ishergin/oxidali/documentation/product-design/bdd/README.md

# BDD

Исполняемые BDD-сценарии — приёмочный канон продукта: поведение собранного
хост-стека, проверенное снаружи.

Границы: в этом каталоге лежит только [реестр ID-префиксов](ids-registry.md). Сами
сценарии — `tests/dali2rust-bdd/features/`; правила слоя (граница чёрного ящика, дерево
фич, теги, трассировка шагов, гейты) — [`05-testing-and-bdd.md`](../../architecture/05-testing-and-bdd.md);
запуск — [`tests/dali2rust-bdd/README.md`](../../../tests/dali2rust-bdd/README.md).
