ishergin/oxidali/documentation/product-design/runtime-modules/mqtt-home-assistant/README.md

# Модуль MQTT Home Assistant

Мост к Home Assistant по MQTT: анонсирует сущности (discovery), публикует их состояние
после коммитов реестра и превращает команды из Home Assistant в семантические команды
шины.

Границы: настройки моста и ручной переанонс — [`../../rest-api/resources/settings-home-assistant.md`](../../rest-api/resources/settings-home-assistant.md);
поведение пары контроллеров — [`../redundancy/README.md`](../redundancy/README.md).
Код — `dali2rust-mqtt-runtime` (воркер, сессия, клиент брокера на ESP-IDF и мок); JSON
Home Assistant строится только в `dali2rust-api/src/ha/`, runtime-крейт несёт готовые
строки.

## Сущности

- Одно устройство Home Assistant на контроллер (`controller_id`). Мост публикует весь
  контроллер: события шины по адаптеру он не фильтрует, адаптер входит в каждый топик.
- **Лампа** — `light` на виртуальную лампу; **группа** — `light` на DALI-группу;
  **выбор сцены** — `select` на адаптер; **устройства ввода** — `event`,
  `binary_sensor` или `sensor` на инстанс, за двумя гейтами: глобальным
  `expose_input_devices` и пер-устройственным `ha_expose`. Физические устройства своих
  сущностей не имеют.
- `unique_id` строится из `controller_id`, адаптера и идентичности ресурса
  (`…_a0_vl_12`, `…_a0_group_7`, `…_a0_scene_select`) и от привязки не зависит:
  перепривязка лампы сущность не меняет.
- Capability группы — объединение по членам; состояние группы сообщает каждый
  цветовой режим, который объявляет её discovery, а у смешанной группы цвет не
  утверждает вовсе.

## Входы и выходы

- **События** (`MQTT_WORKER_HANDLED_EVENTS`):
  `RuntimeStateChangedEvent` — состояние лампы и группы;
  `DaliInputEventObservedEvent` — нажатие или переход датчика;
  `InputDeviceChangedEvent` — переанонс сущностей устройства ввода;
  `PhysicalDeviceChangedEvent`, `VirtualLampChangedEvent` — переанонс ламп (capability
  могли сдвинуться) и пометка групп адаптера;
  `GroupChangedEvent` — переанонс группы; `GroupMatrixChangedEvent` — проход по всем
  группам адаптера (событие не называет, какие сдвинулись);
  `SceneChangedEvent` — переанонс выбора сцены.
- **Команды**: `HomeAssistantDiscoveryPublishCommand` — ручной переанонс (операция
  `ha_discovery_publish`, итог — `HomeAssistantDiscoveryPublishedEvent`);
  `MqttPublishCommand` — публикации правил, за ограничителем (четыре подряд, затем одна
  в секунду; отброшенное считается).
- **Публикует на шину** `DaliSetTargetStateCommand` (лампа, группа) и
  `DaliRecallSceneCommand` (broadcast) с `Origin::Mqtt`: на проводе это `Attended` —
  ползунок web UI обгоняет Home Assistant, а две команды Home Assistant друг друга не
  вытесняют.
- **Триггеры правил** (`when mqtt`): топики мост читает из read-порта стора правил,
  когда сдвигается поколение документа. Сообщение на таком топике — `MqttRuleMessageEvent`
  через `publish_required`, а не команда Home Assistant; топик, который заодно командный,
  — и то и другое ([`ADR-033`](../../../architecture/decisions/ADR-033-mqtt-rule-trigger.md)).
  Темп задаёт мост: не больше одного события на топик за `RULE_MESSAGE_INTERVAL_MS`
  (100 мс) — первое сообщение уходит сразу, следующее ждёт конца интервала, а более новое
  заменяет ждущее. Сообщение не переживает свою сессию: конец сессии выбрасывает и
  ждущее темпа, и то, что ещё стоит в очереди клиента; ждущее выбрасывает и снятие его
  топика из документа. Счётчики блока `mqtt` в `/api/v1/stats`: `rule_messages_total`,
  замещённые `rule_messages_coalesced_total` и потерянные `rule_messages_lost_total` —
  отказ шины после отката или выброшенное сообщение; всё, что не дошло до правил, кроме
  retained-ответа на подписку и потерянного очередью клиента (`commands_dropped_total`,
  §Надёжность), попадает в один из двух последних.
- **Настройки** перечитываются из read-порта, когда сдвигается счётчик применения
  настроек Home Assistant: его двигают запись настроек и перезагрузка слайсов (импорт,
  репликация). На событие настроек мост сознательно не подписан. Пароль брокера —
  отдельный порт.

## Сессия

- **Сессия есть**, только если мост включён, брокер задан и контроллер активен:
  стэндбай и выключенный мост ведут себя одинаково — отключиться, выбросить шину,
  ничего не публиковать. Возврат идёт тем же дозвоном.
- **Переподключает только мост.** Клиент на устройстве — esp-mqtt без обёртки esp-idf-svc
  ([известные дефекты](../../known-issues.md) ISSUE-138), и его собственное
  переподключение выключено: обрыв и неудачный дозвон дают событие отключения, и мост
  звонит заново новым клиентом.
- **Свежая сессия переанонсирует всё**, включая уборку снятых сущностей: retained-
  сообщения — память брокера, а не наша, и брокер без персистентности теряет их при
  рестарте. План тот же, что у ручного переанонса; прерванный обрывом план переносит
  свою операцию в новый прогон. Прогон, который запланировала сама сессия, ни в какую
  операцию не отчитывается и пропускает сущности, уже опубликованные в этой сессии байт
  в байт; ручной переанонс публикует всё заново, не сверяясь с кешем сессии.
- **Смена `controller_id` или префиксов** закрывает сессию: мост публикует `offline` на
  прежнем топике доступности и переанонсирует всё под новыми топиками. Уборка идёт
  только под текущими топиками, поэтому retained-конфиги прежнего `controller_id`
  остаются на брокере осиротевшими: Home Assistant показывает их недоступными, пока их
  не удалят вручную.
- **Топики правил**: свежая сессия подписывает их (QoS 0) следом за командными
  топиками Home Assistant, а смену документа мост досинхронизирует в живой сессии —
  новые подписывает, снятые отписывает. Топик правила, который уже покрывает командный
  фильтр, своей подписки не получает: брокер вправе прислать копию на каждую подходящую
  подписку, и Mosquitto так и делает. Топик, который мост публикует сам (состояние,
  доступность, discovery), он не подписывает вовсе: отказ пишется в лог с топиком,
  считается в `own_topics_refused_total` раз за сессию, сами топики сессии видны в
  `/api/v1/controller`, и флаг `connected` отказ не держит.
  Сообщение, которое брокер доставил с флагом retain, то есть в ответ на саму подписку,
  мост правилам не передаёт (правила —
  [`../rules-engine/mqtt-trigger.md`](../rules-engine/mqtt-trigger.md)).
- **`connected` означает, что брокер может доставить нам всё, на что сессия
  подписывается**: флаг поднимается, когда подписки сессии, топики правил включительно,
  отправлены и подтверждены (SUBACK), а не на CONNACK, и опускается, пока новый топик
  правила ждёт своего SUBACK; SUBACK находит свою подписку по message id. Сверка держится
  на том, что клиент на устройстве выдаёт id по порядку (`CONFIG_MQTT_MSG_ID_INCREMENTAL`
  в `sdkconfig.p4.defaults`): со случайными id две подписки одной сессии, ждущие SUBACK,
  могли бы получить один id, и SUBACK одной закрыл бы другую. Отказ брокера
  в подписке (SUBACK 0x80) держит флаг опущенным, пока отказанный топик остаётся в
  документе правил, а отказ командному фильтру — до конца сессии; каждый отказ
  считается в `subscriptions_refused_total` и пишется в лог с топиком.
- **Доступность**: last will регистрируется в сессии, retained `online` публикуется до
  любого discovery; сознательное отключение сначала публикует `offline`. Лампа объявляет
  два источника доступности — контроллер и себя (`availability_mode: all`), поэтому её
  топик доступности публикуется вместе с конфигом discovery: пока он молчит, Home
  Assistant держит сущность недоступной.
- **Уборка всегда retained**: пустой payload снимает retained-конфиг, только если сам
  несёт флаг retain. Снятие лампы стирает не только её конфиг, но и retained-доступность
  и состояние: лампа, заново созданная под тем же id, иначе унаследовала бы чужие
  `online` и уровень.
- Discovery публикуется размеренно, а не пачкой; переанонс проверяется по хешу, так
  что неизменившиеся конфиги брокер не видит. Глубокий инбокс коалесцирует события по
  сущности.
- Транспорт — `mqtt://` без TLS.

## Граница формата

- **Уровень**: в реестре и на шине — сырой arc power `0..254`; шкала `brightness`
  Home Assistant существует только в MQTT-payload'е, перевод — на границе. Включённая
  лампа с неизвестным уровнем публикуется без `brightness`, а не с нулём; включение
  без яркости — `GO TO LAST ACTIVE LEVEL` в гире.
- **Цветовая температура**: JSON-схема Home Assistant несёт её ключом `color_temp`;
  discovery объявляет `color_temp_kelvin: true`, поэтому значение — в кельвинах. Ключ
  `color_temp_kelvin` в payload'е не читается и не пишется: это имя флага discovery.
  Диапазон `min_kelvin` / `max_kelvin` объявляет только лампа — у группы честного
  диапазона нет.
- Проверки значений — общий разбор уставки, тот же, что у REST.

## Плитка группы

Групповая сущность показывает ON, только если группе **командовали** включение и хотя
бы один её applied-член горит. «Командовали» — групповой или широковещательный факт
питания от нас (Home Assistant, web UI, REST, HCL, правила) или групповой кадр чужого
мастера; broadcast взводит и снимает флаг всем группам; recall сцены и команда только
цвета флаг не трогают. Флаг волатилен: после перезагрузки плитки говорят OFF до первой
групповой команды.

## Надёжность

Доставки at-least-once для discovery и состояния нет: состояние догоняет следующий
коммит, конфиги — хеш-гейт и переанонс свежей сессии. Счётчики — блок `mqtt` в
`/api/v1/stats` и `/api/v1/diagnostics`. `commands_dropped_total` считает всё входящее,
что потеряла очередь клиента (16 сообщений), сообщения на топиках правил тоже: очередь
стоит до разбора топика. Туда же идёт команда Home Assistant, пришедшая в сессии, которая
кончилась до её разбора: после переподключения она не исполняется, как и сообщение для
правил. Сообщение, которое брокер ещё нёс по топику, только что
снятому с подписки, приходит, когда топика уже нет среди правил, и считается принятой
неразмаршрутизируемой командой.

## Тесты

Чёрный ящик через мок брокера (`tests/dali2rust-bdd/features/mqtt_home_assistant/`):
discovery, состояние, команды, цвет, группы, триггеры переанонса; триггер правил
`when mqtt` — в `tests/dali2rust-bdd/features/rules/`. Формат payload'ов —
unit-тесты `dali2rust-api/src/ha/`; сессия и планы — крейт-тесты моста.
