ishergin/oxidali/documentation/product-design/runtime-modules/redundancy/README.md

# Модуль redundancy

Два контроллера на одном сегменте DALI: второй молчит, пока первый жив, и берёт шину,
когда тот перестаёт отвечать. Обнаружение — не наше изобретение: DiiA 351 §7 описывает
единственный арбитраж двух application controller'ов на одном сегменте, который в
экосистеме DALI есть.

Границы: решение и его поправки — [`ADR-018`](../../../architecture/decisions/ADR-018-controller-redundancy.md);
ответ в окне backward-кадра на уровне PHY — [`../../../architecture/08-dali-phy-and-transport.md`](../../../architecture/08-dali-phy-and-transport.md);
REST — [`settings-redundancy`](../../rest-api/resources/settings-redundancy.md),
[`redundancy`](../../rest-api/resources/redundancy.md),
[`policies`](../../rest-api/resources/policies.md),
[`config-transfer`](../../rest-api/resources/config-transfer.md); UI —
[`../../web-ui/redundancy.md`](../../web-ui/redundancy.md). Код —
`dali2rust-redundancy-runtime` (воркер арбитража, супервизор лизы, воркер репликации).

## Роли

351 §5 знает четыре типа устройства, и арбитраж исполняет только type B; types A и C
никогда не спрашивают и не уступают, а лишь отвечают.

| Роль | 351 | Поведение |
|---|---|---|
| `primary` | A / C | не зондирует, активен, пока жив |
| `standby` | B | зондирует, уступает на любой ответ, берёт шину на молчание |

Выборов между равными нет — в спецификации их нет. Пара из двух `standby` допустима и
разводится разницей во времени старта узлов; случайного сдвига нет. Стэндбай, взявший
шину, продолжает зондировать и уступает, как только первичный снова отвечает.
`applicationActive` хранится в NVM, поэтому перезагрузка переключения не отменяет:
погашенный первичный остаётся погашенным, пока его не включат, и обратно не зондирует.

**Сеть роль не двигает.** Воркер арбитража не читает сетевого состояния вовсе:
потеря Ethernet, брокера или HTTP пира роль не двигает ни в какую сторону. Обратное
тоже верно: арбитраж не спасает от отказа блока питания шины, обрыва или замыкания.

## Обнаружение

Стэндбай широковещательно шлёт 24-битный `QUERY APPLICATION CONTROLLER ENABLED` на
приоритете 5 и читает ответ как type B: **любой ответ, включая испорченный**, — у шины
есть хозяин; молчание — нет. Зонд, который не удалось передать (коллизия, занятая
шина), — не молчание и не вердикт. На выключенном адаптере зонд не отправляется вовсе, а
неотправленный зонд — не промах: стэндбай с выключенным адаптером шину не берёт. Почему
не взятие шины по тишине —
[`ADR-018`](../../../architecture/decisions/ADR-018-controller-redundancy.md).

## Ответ

Первичный обязан ответить в окне Table 20. Супервизор заранее кладёт пары «образ кадра →
байт ответа» в таблицу (`dali2rust-platform::arbitration`): это
`QUERY APPLICATION CONTROLLER ENABLED` в широковещательной форме и по собственному
адресу, а без короткого адреса — в форме broadcast unaddressed. Решает задача сниффера,
передаёт прерывание PHY —
[`../../../architecture/08-dali-phy-and-transport.md`](../../../architecture/08-dali-phy-and-transport.md)
§Answering inside Table 20.

Новый запрос — это слот, а не ветвление. Последовательность, чей ответ зависит не от
одного кадра (`READ MEMORY LOCATION` с DTR, `COMPARE` в поиске), таблицей выразить
намеренно нельзя. `applicationActive = false` даёт **пустую** таблицу, а не ответ NO:
NO в DALI — это отсутствие кадра, и потому два стэндбая не могут ответить друг другу и
застыть оба пассивными.

## Лиза живости

Арбитраж доказывает, что жив отвечающий блок, а не что контроллер работает. Поэтому
супервизор раз в секунду продлевает таблицу на 3 с, пока **реестр**, **планировщик HCL**
и **движок правил** провернулись за последние 3 с. Застрявший воркер перестаёт быть
представленным, лиза истекает, ответы прекращаются, и следующий зонд стэндбая находит
шину бесхозной. Механизм отказа — вызов, которого не происходит: ничто ничего не
отзывает, и застрявший супервизор даёт тот же исход. Воркер, который ещё ни разу не
провернулся, живым не считается; воркер в ограниченном ожидании — провернулся: «занят»
не значит «завис». Все читатели лизы берут время у часов супервизора.

`DaliWorker` не наблюдается: на тихой шине он законно спит на инбоксе, а один скан
законно держит его десятки секунд — окно по оборотам либо срабатывало бы на здоровом
скане, либо не значило бы ничего.

Супервизор читает `applicationActive` прямо из хранилища реестра, а не из подписки на
шину: решение раз в секунду обязано приниматься и на насыщенной шине, когда подписка
отстаёт. Событие настроек DALI лишь будит его раньше срока.

## Бюджет времени

| Величина | Формула | По умолчанию |
|---|---|---|
| Обнаружение отказа | порог промахов × период зонда + один зонд | порог 2, период 400 мс: ≤ 0,86 с |
| Переключение роли | флип `applicationActive`, старт HCL и поллера | < 100 мс |
| Плановое переключение | пара `ENABLE`, опрос транслятора, реестр | < 100 мс, свет не меняется |
| Цена провода | ≈ 38 мс активного провода на зонд | ≈ 9,5 % на приоритете 5 |
| Застрявший воркер → молчание | порог застоя + TTL лизы | ≤ 6 с |

Приоритет 5 — самое низкое окно Table 22: зонд уступает всему, что делает оператор.
Порог по умолчанию не выбран — открытый ISSUE-86 в
[`../../known-issues.md`](../../known-issues.md).

## Пассивный контроллер

| Подсистема | На пассивном |
|---|---|
| Провод | любой forward-кадр отказывает `controller_passive` у единственного владельца провода; HTTP отвечает `409 controller_standby` с `Retry-After: 1` |
| Зонд арбитража | идёт — единственное исключение |
| HCL | тик считается, ничего не публикуется |
| Поллер | цикл считается, список целей пуст |
| Мост MQTT | сессии с брокером нет: пара делит `controller_id`, и подключённый стэндбай дрался бы с активным за сущности |
| REST-чтения, WebSocket | работают |

HCL и поллер гасятся ради счётчиков, а не ради провода: провод и так защищён гейтом, а
растущие `command_failures` на правильно себя ведущем контроллере читать невозможно.

**Роль видна** — заголовок и `role` в `/api/v1/health`
([`redundancy`](../../rest-api/resources/redundancy.md)), значок в web UI, буква на OLED
([`display`](../display/README.md)): для звонящего ответы стэндбая истинны и бесполезны,
и без роли «лампа не изменилась» неотличимо от «я говорю не с тем узлом».

## Плановое переключение

Шаги, их порядок и ответы — контракт
[`redundancy`](../../rest-api/resources/redundancy.md) §`POST /redundancy/switchover`.

`Dali103HandoverSentEvent` публикуется до команды ухода в пассив: отдающий узел
записывает переход как `handover`, только если это событие пришло к воркеру арбитража
раньше смены `applicationActive`; принимающий — потому что флаг сдвинул провод. Флаг и
причину его последней смены воркер читает одним вызовом под одной блокировкой
(`application_active_moved_by`): причина, пришедшая событием, отстаёт от флага, и
плановая передача записалась бы как `manual`.

## Перенос конфигурации

Runtime стэндбай получает со сниффера, конфигурацию — с пира (почему так и почему не
MQTT — [`ADR-018`](../../../architecture/decisions/ADR-018-controller-redundancy.md);
что переносится — [`config-transfer`](../../rest-api/resources/config-transfer.md)).
Пассивный контроллер с заданным `peer_url` раз в 30 с тянет у пира манифест слайсов
(`GET /api/v1/config/slices`: имя, размер, CRC), забирает слайсы, чьи размер или CRC
отличаются, кладёт их одной партией в стейдж импорта реестра и публикует **один**
`RegistrySliceReloadCommand` на проход; воркер реестра пишет слайсы, которые
декодируются, и перечитывает реестр, а отвергнутые считает в
`persistence.hydrate_error_total` `/api/v1/diagnostics`
([config-transfer](../../rest-api/resources/config-transfer.md) §Импорт).

- Тянет только пассивный: активный — источник истины пары.
- Порядок пира — порядок гидрации: физические устройства раньше ламп.
- Слайс, которого у пира нет, пропускается, а не удаляется.
- Один reload на проход: reload между двумя слайсами гидрировал бы наполовину
  импортированный набор.
- Недостижимый пир считается и остаётся пиром; роль от этого не меняется.

## Счётчики

Блок `arbitration` в `GET /api/v1/redundancy`:

- `defended` — тики супервизора (раз в секунду), на которых лиза продлена: узел активен
  и все наблюдаемые воркеры крутятся. На пассивном узле не растёт.
- `worker_stale` — тики, на которых лиза не продлена из-за воркера, который встал или
  ещё ни разу не провернулся. Сразу после загрузки счётчик может быть ненулевым: тик
  супервизора успевает раньше первого оборота воркера, и это не отказ.
- `answered` — ответ на чужой зонд дошёл до провода; `suppressed` — зонд узнан и не
  отвечен.
- `cell_busy`, `aborted`, `window_closed` — ответ не ушёл: ячейка PHY занята, передачу
  прервали, окно закрылось; `late` — ответ опоздал.
- `probe_failed` — наш зонд не дошёл до провода; `handover_incomplete` — плановое
  переключение не завершилось.

Журнал переходов (последние восемь, с причинами и метками) — там же, `transitions`.
