ishergin/oxidali/documentation/product-design/runtime-modules/state-fanout/README.md

# Модуль state-fanout

Проектор runtime-фактов: единственный продовый издатель `RegistryRuntimeUpdateCommand`.
Превращает типизированные факты о шине — наша команда исполнена, сцена вызвана, чужой
кадр увиден, устройство прочитано — в коммиты runtime-состояния, раскрывая группы,
broadcast и сцены по участникам.

Границы: как реестр сливает коммит — [`../../../architecture/06-registry-and-persistence.md`](../../../architecture/06-registry-and-persistence.md);
контракт RRUC — [`../../bus-contracts/commands.md`](../../bus-contracts/commands.md)
§Runtime-команды реестра; откуда берутся наблюдения —
[`../sniffer-translator/README.md`](../sniffer-translator/README.md). Код —
`projector_worker` в `dali2rust-fanout-runtime`.

## Входы и выходы

- **Потребляет**: `DaliTargetStateAppliedEvent`, `DaliSceneRecalledEvent`,
  `DaliObservedFrameEvent`, секцию `RuntimeStatus` из `DaliAttributesReadEvent` и
  `DaliAttributeReadOutcomesEvent` (устройство не ответило).
- **Публикует** только `RegistryRuntimeUpdateCommand` и
  `RegistryLevelTransitionCommand`, через `publish_required`. DALI-команд не
  публикует, в реестр напрямую не пишет, активацию сцены не синтезирует.
- **Читает** `ProjectorReadPort`: привязки, applied-членство групп, applied-строки
  сцен, capability ламп.

## Правила раскрытия

| Факт | Раскрытие |
|---|---|
| Наша команда по лампе или короткому адресу | одна запись с обеими идентичностями — один физический коммит |
| Наша команда или чужой кадр на группу | привязанные лампы — **applied**-члены группы |
| Broadcast | все привязанные лампы адаптера |
| Recall сцены (наш или чужой), broadcast | только **applied**-строки сцены; desired-only строки не проецируются |
| Recall сцены на группу | applied-строки сцены, чьи лампы — applied-члены группы |
| Recall сцены на короткий адрес (наш — на лампу — или чужой) | applied-строка лампы, привязанной к адресу |
| Чужой кадр по короткому адресу | лампа, привязанная к адресу, и само устройство |
| Арк-команда без уровня (`LevelTransitionObserved`) | `RegistryLevelTransitionCommand` на каждого участника; уровень считает реестр |
| Секция `RuntimeStatus` чтения | один коммит устройства |
| Исход чтения «устройство не ответило» | наблюдение отсутствия (`device_absent`) без уровня и без `last_seen_ms` |

- **Recall** — наш и чужой — раскрывается из одного `DaliSceneRecalledEvent`: чужой
  `GO TO SCENE` транслятор публикует только этим фактом
  ([`../sniffer-translator/README.md`](../sniffer-translator/README.md)).
- **Цветовой гейт** при раскрытии на разнородных участников —
  [`../../../architecture/06-registry-and-persistence.md`](../../../architecture/06-registry-and-persistence.md)
  §Colour capability gate; capability участника берётся из вида лампы, то есть с учётом
  override устройства.
- **Коалесинг**: подряд идущие наблюдения сниффера с целевым состоянием
  (`TargetStateObserved`) на одну цель `(адаптер, scope, идентичность)` копятся в
  буфере — чужой фейд не заливает инбокс реестра. Новое наблюдение выбрасывает из
  буфера те, что повторяет целиком: уровень, цвет того же режима, факт DAPC и ненулевой
  уровень, от которого реестр ведёт `lastActiveLevel` (102 §9.4). Остальные уходят по
  порядку, каждое своим коммитом со своей меткой, и реестр упорядочивает их против
  собственных коммитов: фейд уровня и цветовой температуры вперемежку сворачивается до
  последнего факта каждого измерения, уровень DAPC и цвет следующего за ним `ACTIVATE`
  приходят оба, затухание до нуля оставляет последний горевший уровень, а цвет группы в
  другом режиме не стирает прежний у участника, который этот режим не принимает. Буфер
  ограничен: переполнение отправляет самое раннее наблюдение. Арк-команды без уровня
  (`LevelTransitionObserved`) не сворачиваются: каждая — отдельный переход. Любой
  другой факт или другая цель сначала сбрасывают буфер, поэтому порядок относительно
  наших фактов сохраняется.
- **Пейсинг**: раскрытие публикуется пачками по восемь с короткой паузой и делит один
  бюджет ретраев на всё раскрытие (`ADR-007`, `ADR-021`).

## Корреляция и источник

- Какие факты несут корреляцию запроса, а какие `CORRELATION_NONE`, и как проброшенная
  монотонная метка упорядочивает наблюдения —
  [`../../../architecture/06-registry-and-persistence.md`](../../../architecture/06-registry-and-persistence.md)
  §Update path и §Merge rules. Метка applied-факта — момент применения на проводе;
  отсутствие не штампуется.
- Источник коммита команды — из её `Origin` (`Api`, `Mqtt`, `Hcl`, `Rules`): `DaliWorker`
  кладёт его в `source` applied-факта и recall-факта рядом с `hold_hcl` команды, и оба
  проектор переносит в каждую запись раскрытия. Наблюдения сниффера — `Sniffer`;
  секция `RuntimeStatus` — `Readback`: чтение ничего не командует, и HCL не должен
  принимать его за ручное вмешательство; отсутствие устройства — `Poller`. Записи без
  команды за спиной `hold_hcl` не снимают.

## `last_dapc_source`

Проектор — единственный, кто его выставляет:

| Факт с DAPC | Значение |
|---|---|
| Наша команда по лампе или короткому адресу | `unknown` (`null` в JSON) |
| Наша или чужая команда на группу или broadcast | `group` |
| Чужой кадр по короткому адресу | `sniffer` |
| Recall сцены | `scene` |

Факт без DAPC (только цвет, только статус) передаёт `None`, и реестр сохраняет
прежнее значение. HCL различает источники по источнику коммита, а не по этому полю.

## Состояние и тесты

Прочного состояния нет, только буфер коалесинга. Чёрный ящик — `SYS-210..215` и
групповой recall (`tests/dali2rust-bdd/features/system/integration-fanout.feature`):
источники API и сниффер. Раскрытие, гейт цвета, `last_dapc_source`, коалесинг —
крейт-тесты `projector_flow.rs` и `sniffer_translator_flow.rs`: канальный уровень
шины чёрному ящику недоступен.
