ishergin/oxidali/documentation/product-design/runtime-modules/apply-orchestrator/README.md

# Модуль apply orchestrator

Исполняет массовое применение: разворачивает его в ячейки по снапшоту реестра и
публикует их по одной, так что размер применения не связан с глубиной очередей шины.
Решение — [`ADR-007`](../../../architecture/decisions/ADR-007-apply-orchestrator.md).

Границы: HTTP-вход применения (`409`, быстрый путь пустого diff, одна execute-команда)
— [`../api-gateway/README.md`](../api-gateway/README.md); жизненный цикл операции —
[`../operation-tracker/README.md`](../operation-tracker/README.md); исполнение ячеек —
[`../dali-worker/README.md`](../dali-worker/README.md). Код —
`dali2rust-operations-runtime` (воркер и ядро пейсинга `apply_pacing`).

## Семейства

| Execute-команда | Снапшот | Ячейка | Исход ячейки |
|---|---|---|---|
| `GroupApplyExecuteCommand` | desired против applied матрицы групп | `DaliProgramGroupMembershipCommand` на одну пару «лампа × группа» | `DaliGroupMembershipProgrammedEvent` |
| `SceneApplyExecuteCommand` | строки одной сцены | `DaliProgramSceneCommand` на одну строку | `DaliSceneProgrammedEvent` |
| `PolicyApplyExecuteCommand` | политика и список известных устройств | `DaliWriteAttributesCommand` с `signals_operation = false` на одно устройство | `DaliAttributesWrittenEvent` |

Ядро пейсинга общее и о семействе не знает; семейство — это тип ячейки и событие её
исхода. Новое семейство обязано объявить событие исхода в подписке оркестратора, иначе
прогон не получит собственных исходов. Событие исхода приходит на каждую исполненную
ячейку, даже когда ничего не подтвердилось, и его ошибка — исход ячейки; у ячейки
политики недостающее значение без ошибки — `verify_failed` (`policy_not_confirmed`).

## Входы и выходы

- **Читает** `ApplyReadPort` — снапшот **в момент дескью** execute-команды, а не в
  момент HTTP-запроса. Правка desired во время долгого прогона оставляет ресурс dirty
  и требует повторного применения.
- **Потребляет** события исходов своих ячеек; статус своей операции не слушает, а
  опрашивает у трекера (ниже, «Отмена»).
- **Публикует** ячейки, синтетические исходы пропуска и провала и терминальный
  `OperationWorkerSignalEvent` — он один заканчивает операцию, исходы только наполняют
  результат. Исходы и сигнал — через `publish_required`: это единственные носители
  итога. Операцию открывает тот, кто просит применение (HTTP, правило, `DaliWorker`
  после discovery), до execute-команды; оркестратор её не открывает.
- **Не делает**: не мутирует реестр (applied выводит реестр из событий исходов), не
  трогает провод (ячейки исполняет `DaliWorker`, поэтому они видны на шине, в
  сниффере и в счётчиках), не считает статус операции (это трекер).

## Пейсинг

- **Привязанная ячейка — окно в одну**: опубликовать ячейку, дождаться её исхода,
  опубликовать следующую. Такт задаёт сам провод DALI; в полёте не больше одной
  ячейки.
- **Непривязанная лампа провода не занимает**: её исход «пропущено» публикуется
  пачками по восемь — меньше любого инбокса событий — и тактируется собственной
  петлёй.
- **Полная ingress-очередь** — ограниченный backoff (десяток попыток до 250 мс).
  Исчерпание проваливает ячейку синтетическим исходом (`cell_ingress_overload`) или
  обрывает пачку пропусков (`skip_ingress_overload`); прогон идёт дальше и
  заканчивается отказом. Это единственная точка backpressure на пути применения.
- **Ячейка без исхода** за 5 с публикуется повторно один раз (запись и readback
  идемпотентны); второй таймаут публикует синтетический провал, чтобы у ячейки был
  исход в результате, и прогон продолжается — одна упавшая ячейка не останавливает
  применение.
- **Отмена**: прогон раз в 250 мс опрашивает статус своей операции у трекера и
  останавливается, как только она терминальна (TTL, отказ доставки, сброс таблицы); есть и
  собственный дедлайн. Почему опрос, а не событие, — `ADR-007`.

## Корреляция

Ячейки несут корреляцию прогона. Поэтому ячейка политики публикуется с
`signals_operation = false`: её сигнал закрыл бы всю операцию после первого
устройства. Операцию закрывает терминальный сигнал оркестратора после последней
ячейки; программирование групп и сцен сигналов не публикует вовсе.

## Состояние

Прочного состояния нет. Прогоны идут строго последовательно в одном потоке, инбокс
исходов перед стартом дренируется, чтобы поздний исход прошлого прогона не засчитался
текущему. Инбокс команд — четыре кадра: переполнение означает затор execute-запросов и
сразу отвечает отказом доставки.

## Тесты

Чёрный ящик: применение, чей diff больше глубины очередей, проходит через пейсинг и
заканчивается `succeeded` с точными итогами (`GRP-066`). Инварианты очереди — одна
ячейка в полёте, петля пропусков, таймаут → повтор → синтетический исход, backoff,
отмена — крейт-тестом `apply_orchestrator_flow.rs`.
