ishergin/oxidali/documentation/product-design/runtime-modules/dali-worker/README.md

# Модуль dali-worker

Единственный владелец провода: исполняет семантические DALI-команды одного адаптера,
решает, кто кому уступает провод, и публикует типизированные факты о том, что
произошло на шине DALI.

Границы: смысл команд — [`../../bus-contracts/semantic-dali-commands.md`](../../bus-contracts/semantic-dali-commands.md);
протокольные правила (приоритет и прерывание, транзакции, чтение ответов, доказательство
DTR, активация цвета) — [`../../../architecture/09-dali-protocol-rules.md`](../../../architecture/09-dali-protocol-rules.md);
доставка отказов, гарантированная публикация и коалесинг —
[`../../../architecture/03-bus-and-backpressure.md`](../../../architecture/03-bus-and-backpressure.md);
PHY и транспорт — [`../../../architecture/08-dali-phy-and-transport.md`](../../../architecture/08-dali-phy-and-transport.md).

## Входы и выходы

- **Команды**: все виды из `DALI_WORKER_HANDLED_COMMANDS` — управление светом,
  программирование, чтение и обнаружение, коммиссионинг gear, Part 103, арбитраж,
  диагностический сырой кадр. Инбокс — 128 кадров.
- **Читает** `RegistryReadPort`: состояние адаптера для гейта, роль контроллера,
  привязку лампы к короткому адресу (в момент исполнения), известные и свободные
  адреса, политику DT8 для конкретного устройства.
- **Публикует** подтверждения запросам, сигналы операций, результаты DALI и
  applied-факты. `RegistryRuntimeUpdateCommand` не публикует никогда: runtime
  доходит до реестра через проектор state-fanout.
- Crate: `dali2rust-dali-runtime` (воркер, семантический исполнитель, `DaliController`).
  Один воркер на транспорт; в прошивке он один.

## Гейты перед проводом

Проверяются в одной точке диспетча, до любого кадра; как отказ доходит до вызывающего и
почему причина названа — 03 §A refusal needs a listener.

- **Адаптер выключен** (`enabled = false`) — отказ `adapter_disabled` любому виду
  команды: каждый из них ведёт провод какого-то адаптера, и тест воркера сверяет список
  отказов с `DALI_WORKER_HANDLED_COMMANDS`.
- **Контроллер пассивен** (`applicationActive = false`) — отказ `controller_passive`
  любой команде, кроме зонда арбитража: пассивный контроллер не передаёт forward-кадров
  (103 §9.9.1), но спрашивать, есть ли у шины хозяин, обязан. Что при этом отвечает
  HTTP — [`../../rest-api/resources/redundancy.md`](../../rest-api/resources/redundancy.md).

## Очередь и приоритет

Перед каждой командой воркер дренирует инбокс и выбирает, что исполнять: по приоритету
вида команды, с уступкой фоновой работы на границе кадра или шага и никогда внутри
начатой транзакции (09). Команды, которые ведут лампу, между собой не
переупорядочиваются
([`ADR-013`](../../../architecture/decisions/ADR-013-wire-priority-and-yield-granularity.md)).

## Коалесинг

В пределах одного дренажа более поздняя команда на ту же цель вытесняет более раннюю;
какие поля вытесненной переходят в выжившую и что получает её вызывающий —
[03](../../../architecture/03-bus-and-backpressure.md) §Coalescing.

- Ключ target-state — `(адаптер, scope, идентичность, hold_hcl)` для лампы, короткого
  адреса и группы; broadcast не коалесцируется. Ключ recall сцены —
  `(адаптер, scope, сцена, идентичность, hold_hcl)`: группа, короткий адрес, лампа или
  broadcast (идентичность 0).

## Part 103 внутри воркера

Коммиссионинг, перечисление инстансов, конфигурация, индикация Part 332 и арбитраж
исполняются здесь же (`dev103`) — модуль [`../input-devices/README.md`](../input-devices/README.md).

## Публикация фактов

Факт, который единственным носит результат (applied-факт, доказательство чтения,
программирование, исход операции), публикуется через `publish_required` с бюджетом на
команду из её приоритета; устройство скана публикуется по мере того, как провод его
описал (03 §Required events, §Producers).

## Тесты

Семантическая команда → ожидаемая последовательность кадров на `MockDaliTransport`,
отсутствие сырого продуктового пути, перепривязка лампы во время полёта. Правила
очереди, коалесинга и бюджетов — крейт-тестами `dali2rust-dali-runtime`.
