ishergin/oxidali/documentation/product-design/runtime-modules/hcl-scheduler/README.md

# Модуль HCL scheduler

Исполняет расписания human-centric lighting: по кривой суток ведёт цветовую
температуру и, если нужно, уровень групп и broadcast на одном или нескольких адаптерах,
уступая ручному управлению до полуночи.

Границы: контракт расписания и его REST — [`../../rest-api/resources/hcl.md`](../../rest-api/resources/hcl.md);
чанковая запись расписаний — [`../../bus-contracts/commands.md`](../../bus-contracts/commands.md)
§Чанковые записи; экран — [`../../web-ui/hcl.md`](../../web-ui/hcl.md). Код —
`dali2rust-hcl-runtime` (планировщик, кривые, астрономия).

## Цели и команды

- Цели — **только группы и broadcast**. Лампу, сцену и сырой кадр HCL не адресует.
- Одно расписание ведёт несколько целей на разных адаптерах; цель-группа раскрывается
  в команду на каждую группу из списка.
- По `level_mode` точки:
  - `absolute` — `DaliSetTargetStateCommand` с уровнем (0 — выключить) и, если задана,
    цветовой температурой в той же команде;
  - `last_active` — `DaliRecallLastActiveLevelCommand` на ту же цель (гир включается
    на свой `lastActiveLevel`), цвет — отдельной командой;
  - `none` — только цвет; цвет лампу не включает, выключенные лампы применят его при
    следующем включении.
- Все команды — `Origin::Hcl`: на проводе `Attended` (ручная команда обгоняет) и класс
  автоматического действия 103 §9.13.1. Покомандного фейда нет — плавность задаёт
  `fadeTime` самого гира.

## Время

Без привязанных часов планировщик не публикует ничего и показывает `time_unsynced`;
часы и часовой пояс — [`../../rest-api/resources/controller.md`](../../rest-api/resources/controller.md)
§`/time`. Восход и закат
считаются локально (NOAA) по координатам расписания; полярный день и полярная ночь
честно дают «нет события», а не выдуманное время. На хосте и в BDD время — управляемый
порт.

## Тик

- Фиксированный тик 60 с; отдельных тиков на астрономических границах нет — минутная
  гранулярность смещений покрывается тиком.
- **Без догонялок**: считается только желаемое состояние на «сейчас»; после загрузки
  или скачка часов пропущенные точки не проигрываются.
- `stepped` — последняя наступившая точка суток, повторно не публикуется;
  `interpolated` — линейная интерполяция между соседними точками по тем значениям,
  которые задают обе; уровень не интерполируется, если соседняя точка — `last_active`
  или `none`.
- Желаемый набор тика самокоалесцируется по `(адаптер, scope, идентичность)` —
  включая broadcast, который исполнитель не коалесцирует, — и публикуется окном в одну
  команду на весь тик, по всем адаптерам: следующая уходит после подтверждения
  предыдущей или его таймаута. Потолок — 32 команды на тик; остаток отбрасывается со
  счётчиком и доигрывается следующим тиком по правилу без догонялок.
- Собственный пейсинг, без операций и без ядра оркестратора.

## Override

- **Триггер** — runtime-коммит (`RuntimeStateChangedEvent`), источник которого не
  `hcl`, не `poller` и не `readback`: ручная команда, Home Assistant, правило, сцена,
  чужой мастер. Чтение ничего не командует и override не ставит. Не ставит его и
  коммит со снятым `commit_holds_hcl`, а снят он только у света правила — действия или
  recall сцены — с `hold_hcl false`: источник у такого коммита честный, `rules`, но
  ручным вмешательством он себя не объявляет.
- **Только по уже ведомой цели**: флаг поднимается для цели, которую расписание сегодня
  уже публиковало, и только расписанию, которое сегодня работает (включено, день
  активен). Иначе ручное «выключить лампу» до первой точки глушило бы расписание на весь
  день, не дав ему отправить ни одной команды. После загрузки и после правки расписания
  цель снова неуязвима, пока по ней не будет публикации. Правка, которую тик уже
  отработал до того, как пришло её событие (тик читает реестр напрямую, событие едет по
  шине), цель не разоружает: публикация по новому определению уже была.
- **Только в ведомой размерности**: свет двумерен. Что заявил коммит, говорит
  `commit_dimensions` события; что ведёт расписание — все его точки: `level_mode` не
  `none` — яркость, есть цветовая температура — цвет. Выключатель на стене не трогает
  кривую, которая ведёт только цвет.
- Лампа коммита сопоставляется с группами цели через `virtual_lamp_id` события. Смысл
  обоих полей — [`../../bus-contracts/events.md`](../../bus-contracts/events.md)
  §`RuntimeStateChangedEvent`.
- **Явная приостановка** — `HclOverrideHoldCommand` от `hcl.hold` из правил. Она не ждёт
  ни публикации цели сегодня, ни пересечения размерностей: каждое расписание, которое
  сегодня работает и ведёт цель, приостанавливается по ней целиком, и после снятия цель
  публикуется заново. Цель держания покрывает то, что приостановили бы коммиты её ламп:
  лампа — цели, куда её ставит правило лампы коммита; группа — себя и цели, куда
  попадает любая её лампа (broadcast и группы, где эта лампа тоже состоит); broadcast —
  все цели адаптера. Без часов команда отвергается (`time_unsynced`).
- Флаг помнит, кто его поднял: лампы коммитов и держаний лампы, группы держаний
  группы, держание broadcast (коммит без лампы считается за broadcast). Флаг гаснет в
  локальную полночь; правка расписания его не снимает. `HclOverrideClearCommand` от REST
  ([`hcl.md`](../../rest-api/resources/hcl.md) §Под-ресурс `/override`) снимает все флаги
  одного расписания. `HclOverrideResumeCommand` от `hcl.resume` из правил снимает на всех
  расписаниях адаптера причины, которые лежат внутри её цели: broadcast — все; группа —
  свою группу и лампы своих членов; лампа — саму себя. Флаг гаснет, когда причин не
  осталось, поэтому `hcl.resume` снимает свой же `hcl.hold`, а флаг, который поднял
  коммит лампы вне цели, остаётся. Команды приходят в ту же воронку, что события, и будят цикл сразу.
- Во время публикации тика всё, что приходит, — команды, коммиты, правки расписаний —
  обслуживается сразу и в порядке входящей очереди планировщика. Внутри канала это —
  порядок публикации, между каналами нет: команда может обогнать событие, опубликованное
  раньше ([03](../../../architecture/03-bus-and-backpressure.md) §Publishing). Коммит
  приостанавливает и цель, которую этот же тик уже опубликовал, а снятие, пришедшее за
  коммитом, снимает и его флаг. Цель, которую держание или коммит приостановили посреди
  тика, этот тик дальше не публикует.
  Правка, сменившая определение расписания под тиком, снимает с плана только его
  команды: остальной план уходит, цели этого расписания снова неуязвимы, а следующий тик
  публикует его новое определение. Такие тики считает `hcl.ticks_cut_total` в
  `/api/v1/stats`.
- Флаги живут в разделяемом журнале: пишет только поток планировщика, HTTP читает.
- Адресной компенсации (обхода приостановленных ламп поштучно) нет.

## Состояние и роль

- Расписания персистятся реестром (`HclSchedules`); состояние планировщика —
  последняя применённая точка, флаги override, время тика — волатильно: после
  перезагрузки тик пересчитывает желаемое на «сейчас».
- На пассивном контроллере тик считается, но ничего не публикуется; во время записи
  прошивки планировщик стоит.
- Счётчики — блок `hcl` в `/api/v1/diagnostics`.

## Тесты

Чёрный ящик (`tests/dali2rust-bdd/features/hcl/`): CRUD, override, runtime поверх
настоящего `PUT /api/v1/time` и кадров мок-транспорта. Ключи коалесинга, потолок тика
и интерполяция с провода не видны — крейт-тесты `dali2rust-hcl-runtime`, включая
сверку восхода и заката с альманахом.
