ishergin/oxidali/documentation/product-design/runtime-modules/input-devices/README.md

# Модуль input devices (IEC 62386-103)

Управляющие устройства DALI-2 — кнопочные панели, датчики присутствия и света,
абсолютные входы — на валидированном 24-битном пути: коммиссионинг, перечисление
инстансов, настройка событий, приём и типизация событий, индикация панелей (Part 332)
и наша собственная роль control device на шине.

Границы: решения — [`ADR-016`](../../../architecture/decisions/ADR-016-input-devices-and-rule-engine.md);
правила провода Part 103 (адресация, кодировки операндов, схемы событий, доказательство
DTR) — [`09-dali-protocol-rules.md`](../../../architecture/09-dali-protocol-rules.md#part-103-control-devices);
REST — [`../../rest-api/resources/input-devices.md`](../../rest-api/resources/input-devices.md);
команды — [`../../bus-contracts/semantic-dali-commands.md`](../../bus-contracts/semantic-dali-commands.md)
§Part 103; приём и типизация событий — [`../sniffer-translator/README.md`](../sniffer-translator/README.md);
события — [`../../bus-contracts/events.md`](../../bus-contracts/events.md)
§Вход Part 103; потребитель событий — [`../rules-engine/README.md`](../rules-engine/README.md);
сущности Home Assistant — [`../mqtt-home-assistant/README.md`](../mqtt-home-assistant/README.md);
арбитраж пары контроллеров — [`../redundancy/README.md`](../redundancy/README.md).
Первоисточники — PDF стандартов в `documentation/IEC62386/` (локально, вне git);
каждое правило ниже сверяется с PDF, а декодер — с кадрами, снятыми с реальной панели.

## Где живёт код

Отдельного runtime-крейта и потока нет (`ADR-016`): коммиссионинг — это семантическая
команда, исполняемая внутри `DaliWorker`, так же как у control gear.

| Слой | Где |
|---|---|
| Адресация, кадр, команды, декодер событий | `dali2rust-domain::dali::dev103` |
| 24-битный обмен | `DaliTransport::exchange_frame24` ([`08`](../../../architecture/08-dali-phy-and-transport.md)) |
| Исполнители команд | `dev103` в `dali2rust-dali-runtime` (скан, коммиссионинг, инстансы, индикация, арбитраж) |
| Приём событий | sniffer translator: декодирует и публикует |
| Записи устройств и инстансов | реестр, слайс `InputDevices` |
| Модель для хоста | `dali2rust-gear-model`: кнопка 301 (переменные таймеров, без их хода), датчик 303, индикация 332 — оракул схем событий и радиокнопок |

## Кадр и события

Три байта: адрес, инстанс, опкод или данные; бит 16 отличает команду (1) от события (0).
Адресное пространство устройств своё, и операнды кодируются не так, как у Part 102
(09).

**Схемы.** Источник события кодируется одной из пяти схем: 0 — тип и номер инстанса,
идентичности устройства нет (заводская); 1 — адрес и тип; 2 — адрес и номер
инстанса; 3 — группа устройств и тип; 4 — группа инстансов и тип. Продукт ждёт схему 2;
как она выставляется и чем законна схема 0 — 09.

**Фильтр событий** — 24-битный контейнер, части 3xx сокращают его ширину. Запрос
отсутствующего старшего байта отвечает NO: это «поля нет», а не ошибка.

**Уведомление о питании** приходит один раз через 1,3..5 с после включения, только
если включено (NVM, по умолчанию выключено).

## Типы инстансов

Какие события присылают кнопка (301), датчики присутствия (303) и света (304) и что из
этого видят правила — цена `double_press`, потеря `long_press_repeat`, переходы и
hold-таймер присутствия, безразмерное значение света —
[`../rules-engine/operations.md`](../rules-engine/operations.md) §1. Сверх этого:

- **Кнопка (301).** Порядок бит фильтра не совпадает с порядком кодов событий.
- **Датчик присутствия (303).** `CANCEL HOLD TIMER` форсирует vacant; его и
  `CATCH MOVEMENT` шлёт движок правил. Отказ сенсора не
  порождает событий — «тихо час» неотличимо от «пусто» без опроса статуса инстанса.
- **Абсолютный вход (302)** — позиция с разрешением, заданным устройством.
- **Мультиплексированные инстансы**: один физический вход бывает выведен двумя-тремя
  инстансами разных типов, и одно нажатие тогда даёт несколько законных событий.
  Коммиссионинг об этом не предупреждает, отдельного счётчика нет, а дедупа в движке
  нет — он был бы догадкой о намерении оператора.

## Коммиссионинг и конфигурация

Порядок: **скан** → **коммиссионинг** (адресация в сессии `INITIALISE` под quiescent
mode, чтобы события не мешали поиску; непрерываем) → повторный скан: инстансы и
возможности, тип — событием каждого ответившего инстанса под его номером →
**конфигурация инстансов** (схема 2, фильтр, группы — каждое поле с read-back'ом) →
выдержка NVM.

- `instanceActive` — единственный бит статуса, который контроллер может писать;
  выключенный инстанс не шлёт событий вовсе.
- **Выдержка NVM**: после изменения NVM-переменной устройству нужно ≥ 30 с питания;
  реестр показывает окно выдержки, а не надеется на него. `SAVE PERSISTENT VARIABLES`
  не используется.
- **Part 333** не реализована
  ([conformance gaps](../../../reference/iec62386-conformance-gaps.md) §9.4): устройство
  может менять свои переменные локально — вплоть до собственного адреса — и сообщает об
  этом событием, но продукт не читает ни это событие, ни флаг локальной настройки. Поле
  `manual_config_active` поэтому всегда `false`, а триггер правил `manual config changed`
  не срабатывает, пока Part 333 не читается; сменённый локально адрес находит только
  повторный скан.
- **Конфликт адресов** детектируется и показывается, а чинится тем же мастером — довод
  против варианта «только приём событий».

## Индикация (Part 332)

- Конфигурация — NVM-переменные видимой индикации (яркость, цвет, тайминг) через
  `PATCH …/instances/{n}/feedback`, каждая с read-back'ом; биты общего цвета и яркости
  делают запись в один инстанс изменением остальных, поэтому после любой записи кэш
  индикации всего устройства сбрасывается. Звуковая индикация не поддерживается.
- **Карта запросов** существует в двух диалектах (исправленная DiiA и первая редакция,
  где запросы коллидировали с блоком `SELECT`); диалект конкретной панели пробуется и
  хранится в её записи. Проба спрашивает исправленный опкод `0x4F` первым, а `0x2F` —
  только после молчания: на панели с исправленной картой `0x2F` — это
  `SELECT FEEDBACK(15)`, команда, а не запрос.
- **Управление** — `ACTIVATE`, `STOP` и `SELECT FEEDBACK` — у движка правил.
  `SELECT FEEDBACK(группа)` одним кадром гасит индикацию у всех инстансов группы,
  кроме тех, чья первичная группа равна выбранной опции: готовые радиокнопки на всех
  панелях набора сразу.
- `feedbackActive` живёт в RAM и после включения питания сброшен, а конфигурация
  переживает: переутверждение — это `ACTIVATE` / `SELECT` по событию power cycle панели
  и по переходу контроллера в активные, а не перезапись.

## Мы как control device

- `applicationActive` (NVM, [`../../rest-api/resources/settings-dali.md`](../../rest-api/resources/settings-dali.md))
  при FALSE оставляет ответы на запросы живыми; это же пассивное состояние стэндбая.
- Мы отвечаем на `QUERY APPLICATION CONTROLLER ENABLED`: type B luminaire по DiiA 351
  через ~10 с после чужого forward-кадра спрашивает, есть ли на шине контроллер, и
  любой ответ гасит его собственный. Погашенный type B продолжает слать события своих
  инстансов, и приёмный путь их принимает. Как ставится ответ —
  [`../redundancy/README.md`](../redundancy/README.md).
- Чего из роли control device ещё нет —
  [`../../../reference/iec62386-conformance-gaps.md`](../../../reference/iec62386-conformance-gaps.md)
  §8 и [`../../roadmap.md`](../../roadmap.md) §R16-C.

## Реестр и персист

До 32 устройств по 32 инстанса, в PSRAM. Что из записи
переживает перезагрузку — [`../../bus-contracts/snapshots.md`](../../bus-contracts/snapshots.md);
почему таймеры инстансов не персистятся —
[`ADR-016`](../../../architecture/decisions/ADR-016-input-devices-and-rule-engine.md)
§Input-device storage.

## Наблюдаемость и тесты

- Блок `input` в `/api/v1/stats`, WebSocket-канал `input` (события и изменения
  записей), строка `IN` на OLED.
- Unit: адресация, 24-битный кодек, декодер — против кадров со стенда.
- Крейт: коммиссионинг на моке, проекция в реестр продакшн-путём
  (`Dali103ScanProgressEvent`, `Dali103InstanceConfiguredEvent`), а не записью в стор.
- BDD (`tests/dali2rust-bdd/features/input_devices/`): HTTP и инъекция 24-битного кадра;
  порядок кадров коммиссионинга — на моке.
- Хост-модель — оракул схем событий и радиокнопок, который стенд с одной панелью дать не
  может.
