ishergin/oxidali/documentation/product-design/runtime-modules/poller/README.md

# Модуль poller

Фоновое чтение известных устройств по интервалу, чтобы runtime-состояние и
доказательства оставались свежими без ручных чтений, — и так, чтобы оператор этого
никогда не заметил. По умолчанию выключен.

Границы: настройки — [`../../rest-api/resources/settings-poller.md`](../../rest-api/resources/settings-poller.md);
приоритет провода и прерывание — [`../dali-worker/README.md`](../dali-worker/README.md)
и [`ADR-009`](../../../architecture/decisions/ADR-009-background-wire-time-budget.md);
счётчики — блок `poller` в [`../../rest-api/resources/diagnostics.md`](../../rest-api/resources/diagnostics.md).
Код — `dali2rust-poller-runtime`.

## Входы и выходы

- **Публикует** `DaliReadAttributesCommand` (`Origin::Poller`, на проводе `Unattended`)
  и `DaliBusHealthProbeCommand` — в тот же инбокс `DaliWorker`, что и все: своей очереди
  у фона нет.
- **Потребляет** `PollerSettingsChangedEvent` (перенастройка без рестарта),
  `RegistrySliceReloadedEvent`, `DaliAttributeReadOutcomesEvent` (закрывает чтение в
  полёте — воркер публикует его всегда, а чанков у «немого» чтения может не быть вовсе)
  и `DaliBusHealthProbedEvent`.
- **Читает** цели опроса через `PollerReadPort` на каждом цикле, а настройки — при
  старте и заново после каждой перезагрузки слайсов: имя в событии перезагрузки называет
  лишь первый из пришедших слайсов, поэтому перечитываются всегда. Между ними настройки
  заменяет `PollerSettingsChangedEvent`.
- **Выключенный адаптер** реестр отдаёт пустым списком целей с `adapter_enabled: false`:
  его устройства не читаются, и health-probe на него не уходит. Провод и так закрыт
  гейтом `DaliWorker`, но отказанное чтение поллер ждал бы до истечения срока.
- **Не публикует** `OperationBeginCommand` (строк в операциях нет) и
  `RegistryRuntimeUpdateCommand`: он только инициирует чтение, runtime доходит до
  реестра штатным путём через проектор. `value_source` таких наблюдений — `poller`.

## Фон не задерживает оператора

Это не настройка: тихое окно, приоритет с прерыванием на границе кадра и бюджет времени
провода —
[`../../../architecture/09-dali-protocol-rules.md`](../../../architecture/09-dali-protocol-rules.md)
§Priority and yielding, решение и его причины — `ADR-009`. Для поллера это значит:
`interval_ms` — пол, а не обещание (растяжку видно по `duty_deferred`), а бюджет
считает всё, что поллер передаёт, включая health-probe, который при этом не занимает
слот чтения.

## Одно чтение в полёте

- Слот освобождают исход чтения, синтетический отказ доставки (инбокс воркера полон)
  и собственный дедлайн чтения.
- **Cooldown — за любое неудавшееся чтение** (аборт по занятости или транспорту,
  неначатое чтение, порванная последовательность): устройство получает
  `3 × interval_ms`. Отсутствующий адрес получает нарастающий cooldown (3, 6, 12
  интервалов), и один ответ его снимает. Прерванное чтение (`preempted`) и потерянный
  исход возвращают цель в очередь без cooldown и считаются отдельно: первое — работа
  механизма приоритета, второе — наша обвязка.
- Ретраи и подтверждение содержимого у фоновых чтений не урезаны: это целостность
  значений, которые видит оператор. Объём фона ограничивает бюджет провода.

## Что читается

- Все известные физические устройства адаптера по короткому адресу; цикл
  **возобновляется после последнего опрошенного**, иначе при бюджете провода хвост
  установки не читался бы никогда. `skip_unbound_virtual_lamps` исключает устройства
  без привязки.
- Группы: `attribute_groups_default` плюс `dt8_color` для устройств с эффективным
  типом DT8 при `include_dt8_color`; `dt6_led` из умолчания читается только у устройств
  с эффективным типом DT6. Цвет сцен поллер не читает никогда. Других исключений по
  устройствам нет.
- Байт отказов Part 207 то же чтение берёт, только когда runtime-секция подозревает
  отказ ([`09`](../../../architecture/09-dali-protocol-rules.md) §Faults and
  identification).
- **Health-probe** сегмента — [`09`](../../../architecture/09-dali-protocol-rules.md)
  §Reading answers; его исходы —
  [`../../rest-api/resources/diagnostics.md`](../../rest-api/resources/diagnostics.md).

**Банки DiiA 252/253** — не больше одной серии на чтение, по тому же бюджету провода.
Серия читается, только если она включена в настройках **и** гир объявил тип 51 / 52:
слепого зондирования нет.

| Серия | Банки | Минимальный интервал |
|---|---|---|
| мощность | 202-204, живая часть | 30 с — чаще гир не обновляет (§9.2.7) |
| энергия | 202-204, накопители | 10 мин |
| диагностика | 205, 206 | 5 мин |
| данные светильника | 207 | один раз |

Из причитающихся серий выбирается самая просроченная; интервал перезапускает только
завершённое чтение. Карта серий волатильна: после рестарта каждая причитается один раз.

## Когда поллер стоит

- Выключен в настройках (умолчание): опрос по умолчанию умножает трафик на шине с
  чужим мастером.
- Контроллер пассивен: цикл считается, список целей пуст.
- Идёт запись прошивки: фон стоит, потому что перезагрузка выбросит прочитанное
  (`ADR-024`).

## Счётчики

Блок `poller` в [`../../rest-api/resources/diagnostics.md`](../../rest-api/resources/diagnostics.md);
как считаются `duty_deferred` и `interactive_deferred` — `ADR-009`.

## Тесты

Чёрный ящик (`tests/dali2rust-bdd/features/poller/`): пропуск непривязанных (только
адресные кадры — probe широковещателен), отсутствие строк операций, `value_source`,
живая перенастройка. Окно, cooldown, выбор групп, серии банков и probe — крейт-тест
`tests/poller_cycle.rs`.
