ishergin/oxidali/documentation/product-design/runtime-modules/rules-engine/README.md

# Модуль rules engine

Локальная автоматика контроллера: связывает события — нажатие кнопки, датчик, время,
изменение состояния, таймер — с действиями над светом, сценами, HCL, индикацией
панелей и MQTT. Работает целиком на устройстве: кнопка меняет свет без брокера, облака
и браузера.

Границы: язык и словарь — [`operations.md`](operations.md), триггер `when mqtt` —
[`mqtt-trigger.md`](mqtt-trigger.md); REST —
[`../../rest-api/resources/rules.md`](../../rest-api/resources/rules.md); экран —
[`../../web-ui/rules.md`](../../web-ui/rules.md); решения —
[`ADR-016`](../../../architecture/decisions/ADR-016-input-devices-and-rule-engine.md);
источник событий входа — [`../input-devices/README.md`](../input-devices/README.md).

## Три крейта

| Крейт | Что в нём |
|---|---|
| `dali2rust-rules-model` | типизированный граф правил, лимиты, трейты `RuleCompiler` и `NameResolver`, serde-проекция для REST; без I/O |
| `dali2rust-rules-lang` | язык v1 (`LANG_RULES_V1 = 1`): лексер и парсер в модель; разбор — рекурсивный спуск с глубиной, которую ограничивает грамматика (`if`, `repeat` и `after` в себя не вкладываются), — он идёт на задаче httpd |
| `dali2rust-rules-runtime` | воркер: приём документа, движок, таймерное колесо, исполнение эффектов; видит только модель, исходника не видит никогда |

Канон — текст оператора, язык заменяем, принтера нет
([`../../../architecture/01-overview.md`](../../../architecture/01-overview.md)
§Crate boundaries that are decisions, `ADR-016`). Хранимый документ несёт `lang_id`,
которым скомпилирован; неизвестный `lang_id` при загрузке гасит правила со счётчиком,
а не паникой. Документ компилируется **целиком**: одна ошибка разбора означает, что не
загружено ни одно правило. `RuleCompiler::compile`
отдаёт только набор, прошедший `dali2rust_rules_model::validate`, и новый язык обязан
вызвать её сам: движок при развороте лишь страхуется — глубину вызова, `repeat`,
вложенность и потолок шагов проверяет снова, а нарушение исполняет как невычислимый
шаг, — и держит бюджет исполненных шагов активации (`partial`). Диапазоны числовых
ссылок (`MAX_LAMP_ID`, `MAX_GROUP_ID`) `validate` не проверяет: язык проверяет их сам, с
координатами числа.

## Входы и выходы

- **Воронка** команд и событий, 128 кадров
  ([`../../../architecture/03-bus-and-backpressure.md`](../../../architecture/03-bus-and-backpressure.md)
  §Capacities).
- **Команды**: `RuleStageCommand` и `RuleCommitCommand` — чанковая запись документа
  (одна замена набора или ничего); `RuleEnableCommand` — бит манифеста без перезаписи
  документа; `RuleRunCommand` — ручной запуск и сухой прогон.
- **События-триггеры**: события входа и служебные события устройств ввода,
  `RuntimeStateChangedEvent` (лампы и агрегаты групп), `DaliSceneRecalledEvent`
  (случившийся recall — наш или чужой, увиденный сниффером), `RedundancyTransitionEvent`
  (`controller becomes active`), `DaliSettingsChangedEvent`,
  `Dali103InstanceConfiguredEvent` (`manual config changed`; не срабатывает, пока флаг
  Part 333 не читается —
  [`../../../reference/iec62386-conformance-gaps.md`](../../../reference/iec62386-conformance-gaps.md)
  §9.4).
- **Сообщения брокера**: `MqttRuleMessageEvent` (`when mqtt`) публикует мост MQTT. Топики
  триггеров мост читает из стора правил, когда сдвигается поколение документа — его
  двигает каждая замена документа, гидрация и перечитка слайсов включительно
  ([`ADR-033`](../../../architecture/decisions/ADR-033-mqtt-rule-trigger.md)).
- **События-инвалидации**: `VirtualLampChangedEvent`, `PhysicalDeviceChangedEvent`,
  `GroupChangedEvent`, `SceneChangedEvent` и `InputDeviceChangedEvent` —
  имя, разрешённое при компиляции, могло перестать разрешаться, и граф
  перекомпилируется; `RegistrySliceReloadedEvent` — слайс-стор сменился под нами
  (импорт или репликация), документ перечитывается и грузится в движок безусловно, а не
  по смене ревизии: у документа пира может быть та же ревизия при других байтах.
- **Публикует** с `Origin::Rules`: `DaliSetTargetStateCommand` и
  `DaliStopFadeCommand` — свет; `DaliRecallSceneCommand` и `SceneApplyExecuteCommand` —
  сцены; `HclOverrideHoldCommand` — `hcl.hold`; `HclOverrideResumeCommand` — `hcl.resume`;
  `HclScheduleEnableCommand` —
  `hcl.enable` / `hcl.disable` (исполняет реестр); `Dali103FeedbackDriveCommand` —
  индикация; `Dali103InstanceActionCommand` — `cancel_hold` / `catch_movement` датчика
  присутствия; `MqttPublishCommand` — `mqtt.publish` (исполняет мост, со своим
  ограничителем); `RulesActivationEvent` на каждую активацию. С `Origin::Api` —
  `RulesChangedEvent` на смену документа и сигнал операции записи через
  `publish_required`.

## Приоритет провода

Световые команды правил — `Interactive`, несветовые действия сохраняют приоритет своего
вида (почему — `ADR-016`, таблица приоритетов —
[`../../../architecture/09-dali-protocol-rules.md`](../../../architecture/09-dali-protocol-rules.md)
§Priority and yielding). В провенансе коммит правила — `rules`, и HCL видит его как
ручное вмешательство, если правило не сказало `hold_hcl false`
([`../hcl-scheduler/README.md`](../hcl-scheduler/README.md) §Override).

## Активация

1. Событие сопоставляется с триггерами включённых правил (до четырёх на правило, между
   ними ИЛИ) в порядке возрастания имени — детерминированно.
2. Cooldown: повтор раньше срока подавляется и считается.
3. Глубина цепочки: активация, вызванная изменением состояния от другой активации,
   несёт глубину на единицу больше; сверх предела — отказ со счётчиком. Это защита от
   петли «правило → свет → то же правило»; сообщения брокера —
   [`mqtt-trigger.md`](mqtt-trigger.md) §Петли.
4. Условия вычисляются по **одному снимку** read-модели: два условия об одной лампе
   видят одно её состояние. С провода движок не читает никогда.
5. Действия исполняются по развёрнутому графу (блоки и `repeat` разворачиваются
   заранее, ветвь `if/else` выбирается по ходу — [`operations.md`](operations.md) §4.6).
   Отказ одного действия не прерывает остальные: исход `partial`.
6. **Световые эффекты на одну цель сливаются поле к полю** до публикации, в позиции
   первого из них: иначе исполнитель вытеснил бы более раннюю команду, а через кадр
   другой цели он её полей не переносит
   ([03](../../../architecture/03-bus-and-backpressure.md) §Coalescing). Сливаются они
   только внутри непрерывной серии световых действий:
   не-световой эффект и `.stop_fade()` закрывают серию, иначе слияние подняло бы более
   поздний глагол раньше них. Эффект с другим `hold_hcl` на ту же цель начинает новую
   уставку: одна команда не объявила бы расписанию два разных решения.
7. Исход — `ok`, `partial`, `failed` или `refused` — ложится в блок `runtime` правила
   (REST), а сама активация — в `RulesActivationEvent`, WebSocket-канал `rules` и
   статистику. Подавленная cooldown или отвергнутая условиями активация исхода и события
   не даёт: её видно лишь по счётчикам.

`wait` и `after` не спят: они порождают континуацию на таймерном колесе, и воркер
возвращается к событиям. Воркер ждёт на инбоксе до ближайшего срока колеса, но не
дольше секунды — расписания по часам и выведенные из снимка переходы остаются живыми,
а отметка живости обновляется и у простаивающего движка.
Сухой прогон (`POST /rules/{name}/run?dry=1`) берёт правило по имени, выключенное тоже,
мимо триггера и cooldown, вычисляет условия и не исполняет ни одного эффекта: итог —
`RulesActivationEvent` с `dry: true`, а не список действий; при невыполненных условиях
события нет, растёт только `conditions_rejected`, а операция всё равно `succeeded`
([`../../rest-api/resources/rules.md`](../../rest-api/resources/rules.md)
§`POST /rules/{name}/run`).

Волатильное состояние движка (cooldown, переменные, таймеры, позиции `scene.cycle`,
фазы `every`, счётчики `stat`) хранится только в упорядоченных контейнерах: порядок
обхода входит в гарантию детерминизма.

Загрузка набора в движок отменяет все ожидающие продолжения и сохраняет по выжившим
именам cooldown, позиции `scene.cycle`, фазы `every` и счётчики `stat`, а переменные и
именованные таймеры — целиком. Кроме перечитывания слайсов, набор грузится в движок
только при смене ревизии документа, а перекомпиляция после переименований в реестре, давшая тот же
граф, ревизию не двигает — ожидающие продолжения её переживают. Переключение одного
правила ревизию двигает, но кладёт бит в движок напрямую, без загрузки набора.

## Хранение

Слайс `Rules` ([`../../bus-contracts/snapshots.md`](../../bus-contracts/snapshots.md)):
манифест с хешем исходника пишется последним, поэтому порванная запись не загрузит смесь
двух документов — гидрация её отвергнет (`rules_banks_torn` в `diagnostic`), и правил не
будет, пока документ не запишут заново. Переменные, таймеры, позиции `scene.cycle` и
последний выбор индикации волатильны (`ADR-016`); режимы после загрузки восстанавливает
правило на `controller starts`.

## Лимиты

Лимиты графа и исходника (правила, блоки, триггеры, условия, действия до и после
разворота, глубина вызова, `repeat`, имена счётчиков `stat`, размер исходника) — константы
`dali2rust-rules-model`, проверяемые после разворота; лимиты исполнения (глубина
цепочки, континуации, переменные, таймеры) — константы движка. У каждого лимита есть
счётчик отказа; ничего не теряется молча.

## Наблюдаемость

- WebSocket-канал `rules`: смены документа и каждая активация.
- Блок `rules` в `/api/v1/stats`: активации по исходам, подавления, отказы условий,
  глубина цепочек, эффекты, континуации (и сколько их ждёт сейчас), задержка от начала
  обработки входа воркером до публикации всех эффектов активации (p50 / p95 / max;
  цель — p50 ≤ 100 мс, p95 ≤ 200 мс), именованные счётчики `stat`.
- Строки `log()` — в журнале контроллера под target `rules`.
- Блок `rules` в `/api/v1/diagnostics`: счётчики воркера.
- Пер-правило: блок `runtime` в проекции REST — сколько раз, когда последний раз и с
  каким исходом ([`../../rest-api/resources/rules.md`](../../rest-api/resources/rules.md)).

## Стек и память

Один поток на `COMMAND_WORKER_STACK` со строкой в бюджете стеков HIL
(`tools/hil/stack_budget.txt`); его глубина растёт с содержимым реестра. Активация
плоская: условия по снимку, действия итератором по развёрнутому графу. Рекурсия
ограничена: разворот углубляется не дальше лимитов графа, а `rule fails` добавляет ровно
один вложенный проход ([`operations.md`](operations.md) §1.7).

## Тесты

- Unit (`rules-model`, `rules-lang`): грамматика на примерах `operations.md`,
  координаты ошибок, разворот и лимиты, тотальность реестра видов
  ([`operations.md`](operations.md), «Расширяемость словаря»).
- Крейт (`rules-runtime`): активация, cooldown, цепочки, континуации, `partial`.
- BDD (`tests/dali2rust-bdd/features/rules/`): HTTP и инъекция кадра в мок-транспорт,
  проверка кадров на моке; событие входа приходит от **настоящего продюсера** —
  транслятор публикует его из инъецированного кадра.
