ishergin/oxidali/documentation/product-design/runtime-modules/sniffer-translator/README.md

# Модуль sniffer translator

Превращает сырые кадры, увиденные на шине от других мастеров и устройств, в
типизированные наблюдения и события входа Part 103. Команд не публикует и ничего не
мутирует.

Границы: приём кадров, кольца и ответ на запрос арбитража в окне backward-кадра —
транспорт и его задача сниффера ([`../../../architecture/08-dali-phy-and-transport.md`](../../../architecture/08-dali-phy-and-transport.md));
что делают с наблюдением дальше — [`../state-fanout/README.md`](../state-fanout/README.md);
контракт событий — [`../../bus-contracts/events.md`](../../bus-contracts/events.md). Код —
`sniffer_translator_worker` в `dali2rust-fanout-runtime`.

## Входы и выходы

- **Вход** — ограниченный канал от транспорта (`DaliTransport::set_observed_frame_sender`):
  чужие 16- и 24-битные forward-кадры и чужие backward-кадры. На хосте кадры
  инъецирует `MockDaliTransport::inject_observed_frame`, а симулированная шина
  dev-сервера играет чужого мастера и панель со своей консоли.
- **Окно сниффера**: каждый сырой кадр сначала зеркалится в WebSocket-канал `sniffer`
  — транслятор единственный видит чужой поток целиком, включая специальные команды и
  запросы, которые типизированная трансляция отбрасывает.
- **Публикует** `DaliObservedFrameEvent` (best-effort), а через `publish_required` —
  три события Part 103 и `DaliSceneRecalledEvent`: нажатие и чужой recall перечитать
  неоткуда.
- **Читает** один узкий порт — тип инстанса устройства ввода
  (`InputInstanceTypeReadPort`): событие схемы 2 называет инстанс, а не его тип.

## Что декодируется

**16 бит**:

- Кадр с адресом unaddressed broadcast (`0xFC`, `0xFD`) доходит только до приборов без
  короткого адреса, а их реестр не описывает: из него не выходит ни наблюдения, ни
  факта, ни цвета DT8, а сам кадр считается отброшенным
  ([`../../rest-api/resources/stats.md`](../../rest-api/resources/stats.md), блок `dali`).
- `DAPC` и `OFF` → `TargetStateObserved` с короткой, групповой или широковещательной
  адресацией; `GO TO SCENE` → recall-факт `DaliSceneRecalledEvent` с источником
  `Sniffer`, без наблюдения: у recall'а один маршрут ко всем потребителям.
- Пара `SET SCENE` или `REMOVE FROM SCENE`, повторённая в окне send-twice без единого
  кадра между половинами (IEC 62386-101 §9.3), → `SceneWriteObserved` или
  `SceneRemovalObserved` с адресом и номером сцены; одиночный или разорванный кадр
  командой не является. Уровень из `DTR0` чужого мастера не доказан, поэтому в
  наблюдение не входит.
- DT8-цвет — с отслеживанием состояния: `DTR` и прелюдия `ENABLE DEVICE TYPE 8`
  запоминаются для всей шины; Tc едет кельвинами сразу. Xy (постановки X/Y) и каналы (RGB
  и WAF, каждая тройка через `DTR0/1/2`) копятся для одного адреса — постановка на другой
  адрес начинает заново — и становятся одним наблюдением на `ACTIVATE`: RGB без WAF —
  `rgb`, с WAF — `rgbwaf`. Каналы декодируются из линейных
  dim level в sRGB
  ([`ADR-022`](../../../architecture/decisions/ADR-022-rgbwaf-channels-are-srgb.md)).
  `ACTIVATE` без поставленного цвета поглощается молча; по чужому адресу или со смесью xy
  и каналов он даёт неоднозначность, а не выдуманный цвет.
- Арк-команды, двигающие уровень без значения (`RECALL MAX/MIN LEVEL`, шаговые,
  `GO TO LAST ACTIVE LEVEL`) → `LevelTransitionObserved`: результат считает реестр.
  `UP` / `DOWN` декодируются и считаются, но не проецируются — стандарт сам не
  предсказывает их результат.
- Всё остальное считается (`unknown_seen`) и **не публикуется**.

**24 бита** (Part 103):

- события инстансов всех пяти схем → `DaliInputEventObservedEvent`; уведомление о
  питании → `DaliInputDeviceLifecycleEvent`;
- чужая пара `ENABLE` / `DISABLE APPLICATION CONTROLLER`, повторённая в окне
  send-twice (105 мс) без единого кадра между половинами (IEC 62386-101 §9.3), →
  `Dali103ApplicationControlObservedEvent` с областью адресации: broadcast, `0xFD` (только
  устройствам без короткого адреса, IEC 62386-103 §9.5.1) или короткий адрес; одиночный
  кадр командой не является;
- прочие команды считаются: командный путь Part 103 принадлежит `DaliWorker`.

## Свойства

- Декодер держит только малое состояние (DTR, прелюдии, пары send-twice), и сам разбор
  не блокируется; публикация обязательного факта на заполненном ingress ждёт по
  ограниченному расписанию `publish_required`
  ([03](../../../architecture/03-bus-and-backpressure.md) §Required events).
- Переполнение входного канала теряет наблюдения со счётчиком и не задерживает
  продуктовый путь.
- `raw_frame` и `decode_status` в событии — диагностическое свидетельство для
  политики потребителя, а не продуктовые данные.

## Тесты

Чёрный ящик: инъекция кадра в мок-транспорт и проверка видимого эффекта (runtime лампы,
активация правила, событие Home Assistant). Правила декодера и публикации — крейт-тесты
`dali2rust-fanout-runtime` и декодер Part 103 в `dali2rust-domain` на кадрах,
захваченных с реальной панели, а не только на собственном кодировщике.
