ishergin/oxidali/documentation/product-design/runtime-modules/websocket/README.md

# Модуль WebSocket

Живая лента для встроенного web UI: клиент подписывается на каналы и получает те же
JSON-формы, что отдаёт REST, без поллинга. Поллинг остаётся запасным путём при обрыве.

Границы: протокол, каналы, пределы клиентов и потери (`DropNotice`) —
[`../../rest-api/resources/websocket.md`](../../rest-api/resources/websocket.md); типы
кадров и почему часть каналов — только триггер перечитывания —
[`../../rest-api/resources/websocket-payloads.md`](../../rest-api/resources/websocket-payloads.md);
поведение клиента — [`../../web-ui/websocket.md`](../../web-ui/websocket.md); отправка на
задаче httpd и разбор кадров на ESP —
[`../../../architecture/02-runtime-and-threading.md`](../../../architecture/02-runtime-and-threading.md)
§WebSocket on the HTTP task. Код — `dali2rust-ws-runtime` (хаб клиентов, воркер,
счётчики, `WsSink`) и `dali2rust-api/src/ws/` (протокол, проекции, снапшоты, батчи
сниффера и логов); в runtime-крейте JSON нет вовсе.

## Входы и выходы

- **Шина**: события из `WS_PROJECTED_EVENTS` — runtime, операции, изменения реестра,
  устройства ввода и их события, документ и активации правил. Набор объявлен рядом с
  таблицей проекции и сверяется с ней тестами.
- **Читает** read-модели статистики и диагностики (каналы `stats` и `diagnostics` —
  периодические снимки, а не события шины), кольцо логов, окно сниффера.
- **Лог**: на устройстве захват идёт через `esp_log_set_vprintf`, поэтому канал `logs`
  видит и C-компоненты ESP-IDF.
- **На шину не публикует ничего** и мутаций не принимает: входящие кадры — только
  подписка и отписка.

## Без клиентов

Воркер паркуется на хабе и не просыпается на события шины. Накопленные события, записи
сниффера и счёт потерь инбокса он сбрасывает до ожидания клиента, а не после: ожидание
возвращается в момент регистрации, и сброс после него съел бы первые события новой
сессии без `DropNotice`. Инбокс воркера — 128 кадров
([`../../../architecture/03-bus-and-backpressure.md`](../../../architecture/03-bus-and-backpressure.md)
§Capacities).

## Наблюдаемость

Блоки `websocket` в `/api/v1/stats` и `/api/v1/diagnostics`.

## Тесты

Чёрный ящик настоящим WS-клиентом (`tests/dali2rust-bdd/features/websocket/`):
подписка, проекции после коммита, отставание и `DropNotice`, сниффер, логи. Кольцо
логов и возврат уровня — крейт-тестами: на хосте стимул недостижим. Разбор кадров на
ESP проверяется только на стенде: хостовый адаптер разбирает их правильно по
построению.
