ishergin/oxidali/documentation/product-design/status.md

# Статус

Что построено, по стадиям. Статус выведен из кода, BDD и экранов web UI.

Границы: оставшаяся работа — [`roadmap.md`](roadmap.md); модули —
[`runtime-modules/README.md`](runtime-modules/README.md); открытые дефекты —
[`known-issues.md`](known-issues.md).

| Стадия | Статус | Что есть |
|---|---|---|
| F0–F1 канон | готово | пакет product-design, `CLAUDE.md` |
| F2 контракты | готово | `dali2rust-contracts::msg`, `declare_bus_payloads!`, замороженный порядок |
| F3 реестр | готово | единый писатель, read-порты, слайс-стор |
| F6 трекер операций | готово | `dali2rust-operations-runtime` |
| R1 адаптеры | готово | список, PATCH, гейт `enabled` |
| R2 физические устройства | готово | четыре ресурса чтения, PATCH, target-state, запись атрибутов, удаление |
| R3 discovery и чтение атрибутов | готово | три режима скана, группы чтения, пресеты банков |
| R4 виртуальные лампы | готово | CRUD, привязка, target-state |
| R5 группы | готово | матрица, apply, target-state |
| R6 сцены | готово | матрицы, apply, recall broadcast и группы, чтение цвета сцен |
| R7 операции | готово | список ключей и детали |
| R9 настройки дисплея | запланировано | — |
| R10 настройки поллера | готово | `/settings/poller` |
| R11 Home Assistant | готово | `/settings/home-assistant`, ручной переанонс |
| R13 диагностика DALI | готово | `/api/v1/dali/*`, `/api/v1/diagnostics`; BDD `DIAG-` |
| R14 статистика | готово | `/api/v1/stats`, экран |
| R15 коммиссионинг gear | готово | identify, смена адреса, замена (группы и сцены заменителя программирует apply), экспертные шаги |
| R16-A 24-битный провод и события | готово | декодер пяти схем, транслятор |
| R16-B устройства ввода | готово | скан, коммиссионинг, инстансы, REST, Home Assistant, экраны |
| R16-C мы как control device | частично | `applicationActive`, гейт TX, ответ на запрос арбитража |
| R16-D индикация Part 332 | готово | конфигурация, управление из правил, модель панели |
| R17-A ответ и лиза | готово | таблица ответов, супервизор |
| R17-B роли | готово | зонд, автомат ролей, `/redundancy`, отказ записи, плановое переключение |
| R17-C перенос слайсов | готово | `/api/v1/config/slices` |
| R17-D репликация | готово | HTTP-pull с пира |
| R17-E политики | частично | `/policies`, применение ко всем и к новому гиру |
| R17-F роль видна | готово | заголовок, `/health`, значок UI, буква на OLED |
| I1 state-fanout и сниффер | готово | `dali2rust-fanout-runtime` |
| I2 поллер | готово | бюджет провода, health-probe, серии банков 252/253 |
| I3 HCL | готово | `dali2rust-hcl-runtime`, override, SNTP и часовой пояс |
| I4 мост Home Assistant | готово | лампы, группы, выбор сцены, устройства ввода |
| I5 WebSocket | готово | двенадцать каналов, до четырёх клиентов |
| I6 кластер | запланировано | — |
| I7 adapter proxy | запланировано | — |
| I8 дисплей | частично | сводный экран без настроек и страниц |
| I9 логи | готово | канал `logs`, экран |
| I10-A язык правил | готово | три крейта, хранение, REST |
| I10-B движок | готово | активации, эффекты, носители всех глаголов, триггер MQTT |
| I10-C экран правил | готово | редактор с автодополнением имён, лента, сухой прогон |
| X1 backpressure | готово | маршрутизация, `publish_required`, коалесинг |
| X2 несколько адаптеров | запланировано | реестр и REST многоадаптерны, исполнитель один |
| X4 гейты стабильности | готово | [`contract-stability-checklist.md`](contract-stability-checklist.md), merge-гейты |

Вне стадий: обновление прошивки по сети (`ADR-024`) и настройки DALI — готово; модель
gear и устройств Part 103 (`dali2rust-gear-model`) для хостового симулятора, хостовых
тестов и эмулятора — готово; эмулятор gear на втором P4 пары (`tools/dali-gear-sim`)
собирается, гейтится и работает на проводе, шаг «тот же гир читает мастер WB» — в долге
стенда ([STRATEGY.md](../../tools/hil/STRATEGY.md) §9.2).
Номера F4, F5, R8, R12 и X3 не используются.

Web UI: панель, лампы, устройства и их детали, устройства ввода, группы, сцены, HCL,
правила, консоль, сниффер, логи, операции, статистика, диагностика, прошивка,
политики, настройки (поллер, DALI, время, Home Assistant, отказоустойчивость).
