ishergin/oxidali/documentation/product-design/web-ui/rules.md

# Экраны: Input devices и Rules

Устройства ввода (`#/input-devices`, `#/input-devices/{sa}[/{n}]`) и документ правил с
живой лентой (`#/rules`).

**Границы:** контракт — [`../rest-api/resources/input-devices.md`](../rest-api/resources/input-devices.md)
и [`../rest-api/resources/rules.md`](../rest-api/resources/rules.md); язык правил —
[`../runtime-modules/rules-engine/operations.md`](../runtime-modules/rules-engine/operations.md);
статистика правил и входа — экран [`stats.md`](stats.md); карточки —
`web/design-system/screens/input-devices.html`, `input-device-detail.html`,
`rules-editor.html`, `components/rule-row.html`, `components/event-feed.html`.

## Устройства ввода

- **Список**: имя, короткий адрес (моно), тип по первому инстансу, присутствие, число
  инстансов, последнее событие. Экран обязан сказать, что **адресное пространство
  отдельное**: панель с адресом 3 и светильник с адресом 3 — не конфликт, но рядом с
  экранами, где короткий адрес всегда означает светильник, это читается именно как
  конфликт.
- Действия: **Scan** (безопасен на живой шине) и **Commission** (назначает адреса,
  держит шину — предупреждение как у control gear). Scan есть и на карточке
  устройства: после перезагрузки карточка пуста до скана, и карточка, которая просит
  скан, должна уметь его запустить.
- **Карточка устройства**: Identify, Forget (запись исчезает, устройство остаётся на
  шине и найдётся следующим сканом), инстансы по вкладкам.

Что карточка обязана показать, иначе оператор увидит неправду (смысл каждого поля — в
контракте input devices):

1. **Цена `double_press`** рядом с флажком: каждое короткое нажатие этой кнопки
  начнёт задерживаться на 0,2–2 с. Это свойство стандарта, молча включать нельзя.
2. **Происхождение значений**: «прочитано · N назад» или пустое «не читалось с
  загрузки» — никогда не ноль.
3. **`manual_config_active`** — плашка «переменные под локальным управлением
  устройства: запись будет отброшена». Пока флаг всегда `false`: Part 333 не
  реализована ([conformance gaps](../../reference/iec62386-conformance-gaps.md)).
4. **Выдержка NVM** — «настройки закрепляются», пока не прошёл `nvm_settling_until_ms`.
5. **Откат схемы событий** (`event_scheme_confirmed: false`) — заметная плашка.

Индикация Part 332 — своя секция: яркость активного и неактивного состояния (цвет
активного — образцом), объявленные возможности и подпись, что горит ли индикатор —
состояние, которое после передёргивания питания панели восстанавливают правила.

## Правила — редактор документа

**Конструктора нет: UI правил — текстовый редактор**, и второго парсера в браузере
нет.

- **Редактор** — текст документа целиком или одного правила (вкладка правила вырезает
  его блок и при сохранении вставляет обратно, не трогая остальные байты: канон —
  исходный текст). Блок — строки от заголовка `rule "…" … {` (скобка на той же строке)
  до строки, где она закрывается; скобки внутри строк и комментариев не считаются. По
  имени блок ищется, только когда правило выбрано или документ сменился не этой
  вкладкой; её собственная правка несёт блок с собой, так что незакрытая на полпути
  строка не выбрасывает вкладку к целому документу. Правило, ушедшее из документа,
  закрывает вкладку насовсем: заголовок с тем же именем, набранный позже, её не
  открывает. Сниппет и заготовка из ленты правят
  документ целиком: сниппет встаёт после открытого правила, и экран переходит к целому
  документу. Счётчик байт против предела документа.
- **Проверка** — `POST /rules/parse` с задержкой после последнего нажатия; ошибка
  подсвечивает строку и колонку. Строка ошибки считается в документе, а подсвечивается в
  том, что показывает редактор: на вкладке правила — от первой строки правила, и ошибка
  вне открытого правила полосы не получает. Оверлей строки ошибки и список автодополнения
  позиционируются константами высоты строки и отступов, которые обязаны совпадать с
  `line-height` и `padding` поля `.rules .code` в `app.css`. Кнопки: «Check», «Dry-run»
  (сухой прогон правила — ничего не исполняет), «Cancel», «Save».
- **Автодополнение имён** — в первом строковом аргументе `lamp("…")`, `group("…")`,
  `input("…", …)` и `hcl.enable("…")` / `hcl.disable("…")` редактор предлагает имена
  реестра: виртуальные лампы, группы, устройства ввода с именем, идентификаторы
  расписаний HCL. Место он узнаёт только взглядом назад от каретки по её строке:
  каретка внутри строкового литерала, а перед его кавычкой — `(` и имя вызова. Смысл
  текста решает разбор на устройстве. Сначала имена с таким началом, потом
  с такой подстрокой, регистр не важен; ↑/↓ — выбор, Enter, Tab или щелчок — вставка
  имени с закрывающей кавычкой, Esc — закрыть, Ctrl+Space — открыть без ввода; каретка,
  ушедшая из аргумента, закрывает список. Имя заменяет весь литерал, только если его
  закрывающая кавычка — своя: последний строковый литерал строки закрыт (кавычка,
  набранная перед существующим кодом, всегда оставляет его открытым), а за кавычкой идут
  `)`, `,`, комментарий или конец строки; иначе имя заменяет лишь набранное от
  открывающей кавычки до каретки, не удаляя код дальше по строке. Имя, которое строка
  языка не вмещает (её
  [лексика](../runtime-modules/rules-engine/operations.md#лексика)), вставляется
  номером — `lamp(12)`, `group(3)`, `input(5, …)`. Номером же, с пометкой о
  неоднозначности, предлагается каждая запись с именем, которое носят несколько записей:
  устройство такое имя отвергает как неоднозначное. Имена читаются при открытии экрана и
  периодической сверкой, а при фокусе редактора, перед открытием списка и при возвращении
  вкладки — заново, если прошлый запрос старше короткого интервала; чаще экран их не
  спрашивает. Четыре вида имён читаются по одному запросу за раз — параллельные
  REST-запросы на единственной задаче httpd заставляют WebSocket-клиента терять кадры
  (ISSUE-39), в том числе кадры живой ленты этого экрана — и независимо: отказ одного
  оставляет этому виду прошлый список и не гасит остальные. Каналов WebSocket ради имён экран не
  подписывает: каждый кадр отправляет единственная задача httpd (ISSUE-39 в
  [`../known-issues.md`](../known-issues.md)), а `virtual_lamps` шлёт кадр на каждое
  изменение света, тогда как имена меняются редко.
- **Сохранение** — `PUT` с `base_revision` версии, на которой построен черновик;
  черновик не трогает ни опрос, ни лента. `409 rule_set_conflict` (другая вкладка
  сохранила раньше) — не общая ошибка, а выбор: «Reload theirs» заменяет черновик, «Keep mine»
  перевзводит сохранение на свежую ревизию, и перезапись требует второго явного
  «Save». О том, что документ изменился на устройстве, экран предупреждает ещё до
  сохранения. `202` — не «сохранено»: проверяется `opCommitted`.
- **Список правил** — имя, переключатель `enabled` (мгновенный `PATCH`), сводка
  правила; выбор правила открывает его в редакторе. Документ, который не действует
  (`diagnostic`), — баннер с причиной: движок не исполняет ни одного правила.
- **Последнее срабатывание** — строка из блока `runtime` под сводкой: счётчик с
  загрузки, задержка, время (метка без привязанных часов — время от загрузки) и
  причина исхода, если она есть; справа — пилюля исхода `ok` / `partial` / `failed` /
  `refused` (`refused` — движок правило не исполнял, пилюля полая). Правило, которое
  ещё не срабатывало, говорит это словами и пилюли не имеет; выключенное правило
  хранит свою последнюю запись.
- **Сниппеты** — готовые примеры из описания языка; набор — в коде экрана.

## Живая лента

Каналы WS `input` и `rules`: время, источник (`dev 3 / in 0`), событие, какое
правило сработало, исход и длительность. Активация приходит на свой канал чуть позже
события, поэтому строка остаётся «нерешённой» около секунды и только потом честно
говорит «no rule fired». Для такой строки есть кнопка «создать правило на это
событие» — она вставляет в редактор готовый `when input(dev=…, inst=…) is …`; это же
рекомендованный способ опознать панель: «нажмите кнопку, которую называете». Исход
активации, прерванной лимитом, показывает причину (условие, бюджет эффектов, глубина
цепочки). Схема 0 в строке — диагноз: у события нет идентичности источника.

Активация приписывается по порядку прихода новейшей нерешённой строке с известным
источником, у которой не истекло окно ожидания: активация идёт за своим событием через
десятки миллисекунд, а нажатия — через секунды, и вне окна это было бы совпадение
(правило по расписанию, старту или лампе своей строки не имеет). Сухой прогон ленту не
трогает.

Янтарный на этих экранах — только у строк, показывающих уровень света; «сработало / не
сработало» — обычная семантика статуса, отставание — `warn`.

## Чем доказан экран правил

Как web UI делит проверку между BDD и своими тестами — общее правило
[05](../../architecture/05-testing-and-bdd.md#layers); для этого экрана:

- **Контракт устройства**, на котором стоит экран, — разбор с позицией ошибки,
  сохранение по `base_revision` и чтение байт в байт, `409 rule_set_conflict`, `PATCH`
  бита `enabled`, запуск и сухой прогон — доказывается чёрным ящиком: BDD-сценариями
  правил на собранном хост-стеке, `RULE-001`…`RULE-009` в
  [`rule-document.feature`](../../../tests/dali2rust-bdd/features/rules/rule-document.feature)
  и `RULE-020`…`RULE-027` в
  [`rule-engine.feature`](../../../tests/dali2rust-bdd/features/rules/rule-engine.feature).
  Тесты web UI его не повторяют.
- **Поведение самого редактора** устройству не видно, и его доказывают тесты web UI
  (гейт `verify_web_assets.sh`) над чистыми модулями `web/app/src/`: `rule-completion.ts`
  — место автодополнения, ранжирование, вставка, клавиши, раскладка и состояние списка;
  `fresh-source.ts` — как часто спрашиваются имена; `rule-extents.ts` — блок правила для
  его вкладки, вклейка обратно и вставка сниппета; `rule-feed.ts` — строки живой ленты,
  приписывание им активаций и заготовка правила; `rule-lexis.ts` — общие для них
  правила [лексики](../runtime-modules/rules-engine/operations.md#лексика) устройства.
