ishergin/oxidali/documentation/product-design/web-ui/hcl.md

# Экран: HCL schedules

Список расписаний HCL (`#/hcl`) и редактор одного расписания (`#/hcl/{id}`).

**Границы:** контракт — [`../rest-api/resources/hcl.md`](../rest-api/resources/hcl.md);
часы — [`../rest-api/resources/controller.md`](../rest-api/resources/controller.md);
исполнение — [`../runtime-modules/hcl-scheduler/README.md`](../runtime-modules/hcl-scheduler/README.md);
карточки — `web/design-system/screens/hcl-schedules.html`, `hcl-editor.html`.

## Общее для страниц

- **Полоса приостановки** под расписанием: «Standing down since HH:MM — {цели} was set
  by hand» и кнопка «Resume now» (`DELETE …/override`). Без неё приостановленное
  расписание выглядело бы так же, как работающее. Состояние приостановки — отдельный
  под-ресурс, поэтому список делает по одному дополнительному `GET` на расписание.

## Список

**Баннер «часы не синхронизированы»** (warn) — из `GET /api/v1/time` (`synced: false`):
без привязанных часов не работает ни одно расписание. Состояние спрашивается у часов, а
не у планировщика. Баннер ведёт на экран Settings → Time (`#/settings/time`), где время и
пояс берутся из браузера или пояс вводится строкой POSIX TZ. Редактор его не показывает.

Карточка расписания: `schedule_id` (моно), переключатель `enabled` (мгновенный
`PATCH`), дни недели, сводка целей по адаптерам, алгоритм, ближайшая точка, статус.
Кнопка «New schedule» создаёт на сервере расписание-шаблон (`POST` без id) и, когда
запись легла, открывает его редактор — id берётся из тела `202`.

## Редактор

- **Точки** — таблица и мини-график суток (уровень — янтарная линия, температура —
  нейтральная). Астрономические точки на график не наносятся: браузер не считает
  положение солнца, и выдуманное время хуже честного «+N точек на восходе/закате».
  Линии рисуют то, что пошлёт планировщик: уровень держится ровно до точки `last_active`
  или `none` и обрывается на ней (к неизвестному концу он не интерполируется), цвет так
  же обрывается на точке без температуры, а у `stepped` линии ступенчатые. После
  последней точки значение держится до полуночи, так что и одна точка — линия. Влияние
  астрономических точек на линии график не показывает. Смена `level_mode` очищает поле,
  запрещённое в новом режиме.
- **Цели** — строки «scope + группы» (адаптер 0); клиент держит только лимит числа
  целей, остальное проверяет сервер.
- **Прочее** — алгоритм с однострочной подсказкой смысла, дни недели, координаты
  (обязательны при астрономических точках — форма это показывает). `enabled`
  переключается в списке.
- Полей плавности **нет**: подсказка отправляет к fade time прибора на карточке
  устройства.
- Сохранение — `PATCH` с массивами целиком; ответ `202` отслеживается как операция,
  и черновик сбрасывается только если запись легла (`opCommitted`). Время, уровень и
  температура зажимаются в допустимый диапазон, когда поле закоммичено; координаты
  проверяет сервер. Отказ сервера (`422`) показывается тостом.
- **Delete** — в два нажатия ([README](README.md) §Правила каждого экрана).
