ishergin/oxidali/documentation/product-design/web-ui/redundancy.md

# Экран: Settings → Redundancy

Настройки и состояние пары контроллеров на одном экране (`#/settings/redundancy`), плюс
индикация роли в сайдбаре и на OLED.

**Границы:** контракт — [`../rest-api/resources/settings-redundancy.md`](../rest-api/resources/settings-redundancy.md)
и [`../rest-api/resources/redundancy.md`](../rest-api/resources/redundancy.md); механизм —
[`../runtime-modules/redundancy/README.md`](../runtime-modules/redundancy/README.md);
карточки — `web/design-system/screens/settings-redundancy.html`,
`components/controller-role.html`.

Настройки и состояние вместе, потому что во время аварии у оператора один вопрос:
настройки говорят, что сконфигурировано, состояние — что произошло. Экран собран из
существующего словаря дизайн-системы. **Роль не берёт янтарный**: активный узел помечен
`ok`, пассивный — обычной поверхностью.

## Карточки

- **Role** — `enabled` и переключатель «This controller is a standby»: значений ровно
  два, поэтому переключатель, а не список; подпись объясняет разницу алгоритмов, а не
  повторяет имя поля.
- **Detection** — период зонда, порог пропусков, адрес пира и **вычисленная** строка
  «Worst-case detection» по формуле контракта: оператор двигает две ручки, а решение
  принимает по третьему числу.
- **Configuration pull** — `peer_url` и строка о направлении: тянет только пассивный
  узел и никогда не толкает — интуиция подсказывает обратное.
- **Now** — ведёт ли узел шину, отвечает ли на зонды прямо сейчас, остаток лизы, счёт
  зондов и подтянутых слайсов, кнопка «Switch over». «Отвечает» и «ведёт» — разные
  строки: на первичном, чьи воркеры встали, первое становится `false` раньше второго.
  Кнопка отключена на пассивном узле, потому что сервер там её всё равно отклонит.
- **Changes of hands** — последние переходы с колонкой «Took» — время переключения из
  записи перехода, а не замер браузера.

При снятом `enabled` внизу висит `warnbar`: ничего не зондирует и не перехватывает, всё
выше — конфигурация на потом.

## Роль вне этого экрана

- **Сайдбар** читает роль из заголовка `X-Dali2rust-Role` любого ответа,
  поэтому индикатор верен и на экранах, ничего не знающих о redundancy. Значок
  показывается **только на стэндбае**: заголовок шлёт каждая сборка, и вечная подпись
  «active» на одиночной установке перестала бы читаться; знать без спроса нужно тот
  случай, когда запись будет отклонена.
- **OLED** — буква роли в строке адреса
  ([`display`](../runtime-modules/display/README.md)).
- **Diagnostics** — карточки Redundancy опрашивают тот же ресурс с частотой экрана: роль,
  таблица арбитража и все счётчики пары на одном экране с `PHY sniffer · Poll fast`,
  чей темп зависит от этой таблицы.
