ishergin/oxidali/documentation/product-design/web-ui/stats.md

# Экран: Stats

Продуктовая сводка контроллера (`#/stats`) — то, что смотрит оператор. Сырые счётчики
по путям остаются на экране Diagnostics.

**Границы:** контракт и смысл блоков — [`../rest-api/resources/stats.md`](../rest-api/resources/stats.md);
карточка — `web/design-system/screens/stats.html`. Что каждый блок `/stats` есть на
экране, проверяет `scripts/verify_read_surface.py`.

## Композиция

1. **Плитки**: аптайм; свободная **внутренняя SRAM** (KiB; при `null` — прочерк «not
   measured on this build»; warn ниже 12 KiB — той же границы, на которой прошивка
   сама предупреждает); идущие операции; **загрузка шины DALI** в процентах с подписью
   «наша доля · чужие кадры» — число устройства, экран его не пересчитывает, и оно
   нейтральное, а не янтарное.
2. **Memory** — внутренняя SRAM подробно (свободно, крупнейший блок, минимум за
   загрузку) и общий 8-битный heap отдельной бледной строкой — почему главное
   число внутреннее, говорит блок `controller` контракта; скрыта, когда поля `null`.
   Крупнейший блок — цифра этапа загрузки, и экран подписывает её «@boot», а не выдаёт
   за текущую.
3. **Bus**, **DALI**, **Operations**, **WebSocket** — строки счётчиков.
4. **Home Assistant bridge** — подключён ли мост показан чипом, а не счётчиком
   (у состояния нет дельты), плюс публикации и их отказы.
5. **Input devices** — блок `input`: события устройств ввода, в том числе без
   атрибуции (схема 0) и от некоммиссионированных устройств, сканы, адресация, отказы
   конфигурации.
6. **HCL** — блок `hcl`.
7. **Rules engine** — блок `rules`: главная метрика — задержка от триггера до
   публикации (p50 / p95 / максимум); превышения глубины цепочки, подавления, отказы
   действий, потерянные продолжения.
8. **Network** — блок `network`; только в сборке, где он есть.

Строки счётчиков и гейджей следуют общему правилу экранов
([`README.md`](README.md) §Правила каждого экрана). Данные — снимок канала `stats`
каждые 5 с, при разрыве — опрос с тем же периодом.
