ishergin/oxidali/documentation/product-design/web-ui/websocket.md

# Живые данные SPA: WebSocket и опрос

Как экраны получают обновления: одно WebSocket-соединение на вкладку, REST как
источник данных и опрос как запасной путь.

**Границы:** протокол и каналы — [`../rest-api/resources/websocket.md`](../rest-api/resources/websocket.md),
типы кадров — [`../rest-api/resources/websocket-payloads.md`](../rest-api/resources/websocket-payloads.md);
реализация — `web/app/src/api/ws.ts` и `useLive` в `web/app/src/hooks.ts`; карточка
индикатора — `web/design-system/components/connection-status.html`.

## Соединение

- Одно соединение на вкладку, открытое до первого рендера и живущее при смене экранов:
  контроллер обслуживает всего четыре клиента.
- Подписка считается по ссылкам: несколько экранов могут хотеть один канал, и
  отписывается последний ушедший. Для `sniffer` это и есть выключатель тапа на
  устройстве. После `hello` (и после каждого переподключения) клиент заново шлёт
  подписку; уровень лога едет в ней же.
- Переподключение: 1 → 2 → 4 → 8 → 15 с. Отказ по ёмкости (CLOSE `1013`) — ждать не
  меньше минуты: контроллер жив и просто раздал все сокеты, а каждое рукопожатие
  стоит времени его единственной задачи httpd. Окончательный отказ — CLOSE `1008`
  (чужой `Origin`): клиент больше не переподключается, экраны опрашивают.
- Лестницу сбрасывает приветствие `hello`, а не открытие сокета: отказ по ёмкости
  приходит уже после апгрейда, и сброс на открытии держал бы клиента на первой ступени.

## Экраны

- Данные всегда читаются по REST, а кадры канала — **триггеры** перечитывания (кроме
  экранов, чьи кадры и есть данные: сниффер, лог, лента правил, снимки `stats` и
  `diagnostics` — их форма та же, что у REST). Поэтому форма данных в приложении одна,
  есть сокет или нет.
- Пока соединение живо, опрос экрана растягивается до сверки раз в 60 с; при разрыве
  возвращается к своему периоду (обычно 5 с). После восстановления соединения экран
  перечитывается один раз: то, что изменилось за разрыв (например, перезагрузка
  контроллера), иначе провисело бы под зелёной точкой до сверки. Смена периода опроса
  данные экрана не сбрасывает — их сбрасывает только смена ресурса; иначе каждый переход
  соединения возвращал бы экраны в «Loading…».
- Перечитывание по триггерам ограничено по частоте (не чаще раза в секунду после
  первого, с короткой задержкой): apply на тысячу ячеек шлёт событие на строку, а
  каждый запрос — окно, в котором задача httpd не обслуживает никого другого.
- `DropNotice` с `channel: "*"` перечитывает ресурсы всех каналов подписки.
- Скрытая вкладка сокет держит, но не перерисовывается: перечитывание **записывается
  как долг** и выполняется при возвращении вкладки — у канала нет replay.

## Индикатор соединения

Точка в сайдбаре рядом с переключателем темы: `Live` (зелёная), «Reconnecting»
(warn, экраны пока опрашивают; пульсирует только это состояние — мигание должно
значить «нужно внимание»), `Offline` (красная, больше минуты без соединения), `Refused`
(красная полая: CLOSE `1008`, повторов не будет). Причина — в подсказке.
Никогда не янтарная.
