ishergin/oxidali/documentation/product-design/web-ui/lamp-state.md

# Компонент: ячейка состояния лампы

Что означает кольцо «не подтверждено» (`.unconfirmed`) в ячейке состояния лампы на
экранах устройств и ламп.

**Границы:** семантика `value_source` и `status` —
[`../rest-api/contracts/state-contracts.md`](../rest-api/contracts/state-contracts.md);
настройка поллера — [`../rest-api/resources/settings-poller.md`](../rest-api/resources/settings-poller.md);
карточка — `web/design-system/components/lamp-state.html`.

## Задача

Команда уровня в DALI **не подтверждается**: у DAPC нет обратного кадра. Уровень,
отправленный прибору без питания, уходит в провод, эхом попадает в реестр и ничем не
опровергается. Нарисовать его так же, как прочитанный с прибора, — значит заявить
наблюдение, которого не было.

## Правило

Кольцо значит **«не проверено»**, а не «ещё не перечитано». Оба условия обязательны:

1. значение произвела не читалка — `value_source` не `poller`;
2. и читалки не будет — опрос выключен.

Без второго условия кольцо загоралось бы на каждой лампе, которой оператор коснулся на
исправной шине, на время до следующего чтения поллера: разрыв, который закрывается
сам, — это обои, а не сигнал. При выключенном опросе разрыв не закрывается никогда, и
кольцо — единственное, что об этом говорит.

Прибор, который действительно перестал отвечать, к кольцу отношения не имеет: его
несёт перечёркнутая точка `device_absent`, и она старше по приоритету.

До первого ответа флаг «опрос включён» считается истинным, а неудачное чтение
настроек оставляет прежнее значение: кольцо не вспыхивает на каждой перезагрузке
страницы.

Опрос по умолчанию выключен, поэтому свежий контроллер показывает кольца. Это честно:
показанные числа действительно только скомандованы. Оператор снимает кольца, включив
поллер, — то есть заведя то, что будет их проверять.

## Чего правило сознательно не делает

- **Не смотрит на `status`.** Он отвечает «отвечал ли прибор хоть раз за загрузку», а
  не «отвечал ли после команды» (state-контракты, §`RuntimeObservation`): одно нажатие
  «Read attributes» гасило бы кольцо до конца загрузки.
- **Не заводит поле в состоянии.** «Опрос включён» — настройка контроллера, одна на
  всех; на поустройственном payload она размножилась бы по каждому устройству каждого
  кадра и менялась бы без изменения состояния. Настройка и состояние соединяются в
  презентации.
- **Не учитывает охват поллера.** Фильтр непривязанных устройств и маска групп могут
  исключить конкретный прибор при включённом опросе — он будет выглядеть проверяемым.
  Приближение осознанное: точный ответ потребовал бы класть охват в тот же
  поустройственный payload, который предыдущий пункт запрещает.
- **Не заменяется одной плашкой на экран.** «Опрос выключен: состояния скомандованы»
  вверху страницы — второй механизм того же факта, и он теряет главное: точка стоит
  рядом с числом, которому оператор собирается поверить.
