ishergin/oxidali/documentation/product-design/runtime-modules/registry/read-port.md

# Read-порт реестра

Контракт чтения реестра для остальных модулей: что порт гарантирует и почему он
разрезан на узкие трейты. Методы — трейты в `dali2rust-domain::registry`, они и есть
канон; здесь только правила.

Границы: блокировка и владение — [`../../../architecture/06-registry-and-persistence.md`](../../../architecture/06-registry-and-persistence.md);
стек задачи httpd и размеры видов — [`../../../architecture/07-memory-and-cores.md`](../../../architecture/07-memory-and-cores.md).

## Разрез

- **`RegistryReadPort`** — минимальный трейт исполнителей: состояние адаптера для
  гейта, роль контроллера, привязка лампы к короткому адресу, известные и свободные
  адреса, пер-устройственная политика DT8. Никаких тяжёлых видов: `DaliWorker` и
  проектор не должны от них зависеть.
- **Узкие порты под потребителя**: адаптеры, физические устройства (сводка, ядро,
  одна секция атрибутов, покрытие банков), лампы, группы, сцены, настройки, проекции
  Home Assistant, цели поллера, снапшоты применения, тип инстанса устройства ввода.
  Потребитель получает ровно тот порт, которым пользуется.
- Полный вид физического устройства и счётчики применения (apply-watch) на портах
  чтения не лежат — [`06`](../../../architecture/06-registry-and-persistence.md)
  §Ownership and locking.

## Гарантии

- Одно чтение — согласованный снимок под блокировкой стора; между двумя чтениями
  одного потребителя транзакции нет. Привязка может измениться между двумя вызовами,
  поэтому исполнительные пути (`DaliWorker`, оркестратор, проектор) читают
  идентичность как можно ближе к моменту исполнения.
- DTO, собранный из нескольких чтений, — eventually consistent read-модель.
- Несуществующий ресурс — `Option` или минимальный снимок по контракту метода;
  интерпретирует его граница вызывающего.

## Чего порт не делает

Не пишет, не публикует команд, не считает diff desired против applied, не трогает
провод и не скрывает гонку между независимыми чтениями.
