ishergin/oxidali/documentation/product-design/runtime-modules/operation-tracker/README.md

# Модуль operation tracker

Ведёт долгие работы, на которые маршрут ответил `202` и `operation_id`: принимает
начало, собирает исходы, переводит статус и отдаёт read-модель `GET /api/v1/operations`.
Бизнес-логики discovery, чтения или применения не содержит.

Границы: REST-контракт операций — [`../../rest-api/resources/operations.md`](../../rest-api/resources/operations.md);
какие команды открывают какой тип — [`../../bus-contracts/commands.md`](../../bus-contracts/commands.md)
§Команды и операции; развёртка массового применения —
[`../apply-orchestrator/README.md`](../apply-orchestrator/README.md). Код —
`dali2rust-operations-runtime`.

## Типы операций

Типы, статусы, TTL и срок хранения — внешний контракт
([`../../rest-api/contracts/enums.md`](../../rest-api/contracts/enums.md),
[`../../rest-api/resources/operations.md`](../../rest-api/resources/operations.md)).

Три активности коммиссионинга взаимно исключают друг друга на адаптере: HTTP
проверяет все три типа, прежде чем начать любую. Проверка «на этом адаптере» идёт по
ключу, а не по `target_adapter_id` (это id шины): ключ операции применения групп и сцен
и трёх типов коммиссионинга начинается с `<семейство>-<адаптер реестра>-`, и гейт `409`
сверяет этот префикс — смена формата ключа в HTTP-хендлерах молча выключает гейт.

## Входы и выходы

- **Команды**: `OperationBeginCommand` (открыть строку: ключ, тип, адаптер, TTL) и
  `OperationRegistryResetCommand`.
- **События**: `OperationWorkerSignalEvent` — начало, успех или отказ работы;
  события-исходы, которые наполняют результат: ячейки групп и сцен, разбор чтения
  атрибутов по группам, итоги коммиссионинга, итог переанонса Home Assistant.
- **Подтверждения**: собственный инбокс. Синтетический `DeliveryRejected` на
  correlation открытой операции проваливает её сразу с `commands_ingress_overload`
  ([`../../../architecture/03-bus-and-backpressure.md`](../../../architecture/03-bus-and-backpressure.md)
  §A refusal needs a listener).
- **Публикует** `OperationStatusChangedEvent` на каждый переход.
- **Read-модель**: `GET /api/v1/operations` — ключи; `GET /api/v1/operations/{id}` —
  типизированный вид с терминальной ошибкой и результатом.

## Жизненный цикл

Статусы и видимые клиенту правила — REST-ресурс операций. Внутри трекера:

- Операция заканчивается сигналом исполнителя, отказом доставки, вытеснением, сбросом
  таблицы (`OperationRegistryResetCommand`; продового издателя нет) или своим TTL. Чем
  кончилась сама работа, сообщает только сигнал, поэтому каждый сигнал публикуется через
  `publish_required`; исходы наполняют результат и операцию не заканчивают.
- Сигнал, исход или отказ доставки, обогнавший `OperationBeginCommand`, буферизуется (ограниченно и
  с собственным сроком) и применяется, когда строка появится; сигналы чтений поллера,
  у которых начала нет вовсе, штатно отбрасываются.
- Вытеснение и сброс — только запись в таблице (`cancelled` с `superseded` или
  `registry_reset`): отмены на проводе нет, уже опубликованная команда исполняется до
  конца; прогон применения опрашивает статус и останавливается. Какие операции не
  вытесняются — [`operations.md`](../../rest-api/resources/operations.md).
- Детали результата применения групп и сцен (запрограммировано, пропущено, провалено)
  капируются 128 строками на корзину; точные итоги `*_total` всегда полны. У
  применения политики счёта исходов и результата нет.

## Тесты

Чёрный ящик: список и детали операций, отсутствие строки у target-state
(`tests/dali2rust-bdd/features/operations/`). Жизненный цикл, отказ, TTL, вытеснение,
сброс и удаление после срока хранения — крейт-тестом `operation_tracker_flow.rs`:
публикация кадров шины чёрному ящику недоступна.
