ishergin/oxidali/documentation/product-design/rest-api/resources/operations.md

# Ресурс: Operations

Чтение состояния долгих операций — всего, что маршрут принял ответом `202` +
`operation_id`.

**Границы:** какие маршруты создают операции и почему —
[`../stability-and-versioning.md`](../stability-and-versioning.md) §Дисциплины ответа;
типы, статусы и исходы чтения — [`../contracts/enums.md`](../contracts/enums.md);
коды ошибок — [`../contracts/error-dto.md`](../contracts/error-dto.md); трекер —
[`../../runtime-modules/operation-tracker/README.md`](../../runtime-modules/operation-tracker/README.md).
BDD — [`operations`](../../../../tests/dali2rust-bdd/features/operations/).

## Маршруты

| Метод | Путь | Ответ |
|---|---|---|
| `GET` | `/api/v1/operations` | `{"operations": [<operation_id>…]}` — только ключи, без фильтров и пагинации |
| `GET` | `/api/v1/operations/{operation_id}` | `OperationView` или `404 not_found` |

Оба читают одну ограниченную таблицу трекера. Живой поток переходов — канал WebSocket
`operations`; что несёт его кадр — [`websocket-payloads.md`](websocket-payloads.md).

## `OperationView`

- `operation_id` — строковый ключ (`pd-attr-0-17-42`, `firmware-update`, …), `type`,
  `status`.
- В терминальном статусе — `error {code, message}` при отказе; `result` для apply,
  commissioning и HA discovery (`entities_published` / `entities_failed`);
  `attribute_read_outcomes` для чтения атрибутов. Поля есть только когда применимы;
  вариант `result` различается набором ключей.
- `result` apply групп и сцен — точные итоги по ячейкам (запрограммировано,
  пропущено, отказало и т. п.); `result` каждой процедуры commissioning — в
  [`commissioning.md`](commissioning.md).

## Жизненный цикл

- `accepted` → `running` (владелец начал работу) → `succeeded` / `failed`.
- `succeeded` не значит, что реестр уже спроецировал результат: терминальный сигнал
  трекера и проекция в реестр — разные подписчики шины, и последний исход применения
  групп или сцен может дойти до реестра позже сигнала. Клиент перечитывает ресурс
  (`applied`), пока результат не появится, а не читает его один раз.
- `timed_out` — терминального сигнала не было за TTL операции. TTL зависит от типа
  работы: по умолчанию 10 мин, discovery — выведен из худшего числа кадров скана,
  `config_write` — 10 с (это обход реестра, а не прогон DALI), `firmware_update` —
  5 мин. Конфигурация инстанса и индикации устройства ввода — тоже `config_write`, но
  идёт по проводу и ждёт как работа на проводе, 10 мин.
- `accepted` → `failed` с `commands_ingress_overload` — команда операции не была
  доставлена владельцу. Это немедленный отказ, а не таймаут: имеет смысл повторить.
- `cancelled` — только автоматическая отмена: операцию вытеснила новая того же типа над
  тем же ресурсом (`superseded`): ресурс — ключ операции без последнего сегмента, то есть
  адаптер у скана и прибор у чтения или записи атрибутов. Не вытесняются `config_write` и
  применения: их оркестратор исполняет по одному, и новое ждёт очереди; не вытесняется и
  коммиссионинг: две его операции разводит исключение на адаптер, а не отмена. Ещё отмена —
  сброс таблицы операций (`registry_reset`; издателя сброса в проде нет). Отмена —
  только запись в таблице: уже опубликованная команда исполняется до конца, и её исход
  операция не покажет; прогон применения, заметив отмену, останавливается. Публичной
  отмены нет.
- Завершённая операция хранится 60 с, затем `GET` отвечает `404`. Клиент различает
  «ещё не видна» (сразу после `202`, продолжать опрос) и «уже вытеснена из таблицы».
- `firmware_update` при успехе заканчивается перезагрузкой контроллера, и таблица
  операций не переживает её: исход обновления читается из
  [`firmware.md`](firmware.md), а не из операции.

## Что операций не создаёт

Target-state, вызов сцены, expert-шаги commissioning и прочие синхронные маршруты:
их исход — ответ на сам запрос. Фоновые чтения поллера тоже не создают строк.
