ishergin/oxidali/crates/dali2rust-hcl-runtime/src/runtime/scheduler_worker.rs

use std::collections::HashMap;
use std::sync::atomic::{AtomicU32, Ordering};
use std::sync::{Arc, Mutex, MutexGuard};
use std::time::{Duration, Instant};

use dali2rust_bsp::stack_probe::StackLowWater;
use dali2rust_bsp::{esp_thread, std_thread_stack};
use dali2rust_bus::{
    publish_or_drop, BusChannel, BusFrame, BusId, BusPublisher, BusSubscriberRx,
    CorrelationIdAllocator, PublishResult,
};
use dali2rust_contracts::bus::{
    build_confirmation_envelope, build_confirmation_envelope_with_product_error, command_envelope,
};
use dali2rust_contracts::msg::{
    BusCommandPayload, BusEventPayload, DaliRecallLastActiveLevelCommand,
    DaliSetTargetStateCommand, DeliveryStatus, ErrorCode, HclOverrideClearCommand,
    HclOverrideHoldCommand, HclOverrideResumeCommand, HclScheduleChangedEvent, Origin,
    RuntimeStateChangedEvent,
};
use dali2rust_contracts::SOURCE_ID_UNSPECIFIED;
use dali2rust_domain::registry::{HclScheduleView, HclSchedulerReadPort};
use dali2rust_platform::small_sort::insertion_sort_by;
use dali2rust_platform::wall_clock::{LocalCivilTime, WallClock};

use super::astronomy::Location;
use super::curve::{effective_points, evaluate, DesiredState};
use super::overrides::{
    commit_hits_target, driven_dimensions, hold_covers_target, resume_removal, Causes,
    OverrideLedger, RuntimeCommit,
};
use super::plan::{
    coalesce, expand_target, plan, DesiredEntry, PlannedCommand, TargetKey, TickPlan,
};

pub const DEFAULT_TICK_PERIOD_MS: u64 = 60_000;
pub const DEFAULT_COMMAND_TIMEOUT_MS: u64 = 2_000;
const MAX_IDLE_WAIT: Duration = Duration::from_secs(1);
const CONFIRMATION_POLL_SLICE: Duration = Duration::from_millis(50);
const DAYS_PER_WEEK: u8 = 7;
const HOLD_WITHOUT_CLOCK: &str = "time_unsynced";

#[derive(Clone, Copy, Debug)]
pub struct HclConfig {
    pub tick_period_ms: u64,
    pub command_timeout_ms: u64,
}

impl Default for HclConfig {
    fn default() -> Self {
        Self {
            tick_period_ms: DEFAULT_TICK_PERIOD_MS,
            command_timeout_ms: DEFAULT_COMMAND_TIMEOUT_MS,
        }
    }
}

#[derive(Debug, Default)]
pub struct HclSchedulerCounters {
    pub ticks: AtomicU32,
    pub ticks_time_unsynced: AtomicU32,
    pub commands_published: AtomicU32,
    pub commands_dropped_cap: AtomicU32,
    pub command_timeouts: AtomicU32,
    pub command_failures: AtomicU32,
    pub ingress_rejections: AtomicU32,
    pub overrides_started: AtomicU32,
    pub overrides_cleared: AtomicU32,
    pub overrides_reset: AtomicU32,
    pub ticks_cut: AtomicU32,
    pub ignored_events: AtomicU32,
    pub ignored_commands: AtomicU32,
}

pub const HCL_SCHEDULER_HANDLED_EVENTS: &[&str] =
    &["HclScheduleChangedEvent", "RuntimeStateChangedEvent"];

pub type SharedOverrideLedger = Arc<Mutex<OverrideLedger>>;

pub(crate) fn lock_ledger(ledger: &SharedOverrideLedger) -> MutexGuard<'_, OverrideLedger> {
    ledger.lock().unwrap_or_else(|poisoned| poisoned.into_inner())
}

struct PublishRecord {
    state: DesiredState,
    confirmed: bool,
}

#[derive(Default)]
struct PublishOutcomes {
    entries: Vec<(TargetKey, bool)>,
}

impl PublishOutcomes {
    fn merge(&mut self, key: TargetKey, confirmed: bool) {
        match self.entries.iter_mut().find(|(k, _)| *k == key) {
            Some((_, all)) => *all &= confirmed,
            None => self.entries.push((key, confirmed)),
        }
    }

    fn demote(&mut self, key: TargetKey) {
        if let Some((_, confirmed)) = self.entries.iter_mut().find(|(k, _)| *k == key) {
            *confirmed = false;
        }
    }

    fn get(&self, key: &TargetKey) -> Option<bool> {
        self.entries.iter().find(|(k, _)| k == key).map(|(_, c)| *c)
    }
}

struct SchedulerState {
    last_published: HashMap<TargetKey, PublishRecord>,
    published_from: Option<Vec<HclScheduleView>>,
    tick: Option<TickScope>,
}

#[derive(Default)]
struct TickScope {
    sources: Vec<(TargetKey, String)>,
    published: Vec<TargetKey>,
    stood_down: Vec<TargetKey>,
    edited: Vec<String>,
    cut: bool,
}

impl TickScope {
    fn planned(schedules: &[HclScheduleView], fresh: &[DesiredEntry]) -> Self {
        let source = |entry: &DesiredEntry| schedules.get(entry.schedule).map(|view| view.schedule_id.clone());
        let sources = fresh.iter().filter_map(|entry| Some((entry.key, source(entry)?))).collect();
        Self { sources, ..Self::default() }
    }

    fn planned_by_an_edited_schedule(&self, target: &TargetKey) -> bool {
        self.sources
            .iter()
            .any(|(key, schedule)| key == target && self.edited.contains(schedule))
    }
}

impl SchedulerState {
    fn new() -> Self {
        Self {
            last_published: HashMap::new(),
            published_from: None,
            tick: None,
        }
    }

    fn stand_down(&mut self, target: TargetKey) {
        self.last_published.remove(&target);
        if let Some(tick) = self.tick.as_mut() {
            tick.stood_down.push(target);
        }
    }

    fn note_published(&mut self, target: TargetKey) {
        if let Some(tick) = self.tick.as_mut() {
            tick.published.push(target);
        }
    }

    fn driven(&self, target: &TargetKey) -> bool {
        self.last_published.contains_key(target)
            || self.tick.as_ref().is_some_and(|tick| tick.published.contains(target))
    }

    fn skips_in_tick(&mut self, target: &TargetKey) -> bool {
        let Some(tick) = self.tick.as_mut() else {
            return false;
        };
        let cut = tick.planned_by_an_edited_schedule(target);
        tick.cut |= cut;
        cut || tick.stood_down.contains(target)
    }

    fn edit_during_tick(&mut self, edited: &str, current: &[HclScheduleView]) {
        let was = self.published_from.as_deref().and_then(|views| schedule_named(views, edited));
        let now = schedule_named(current, edited);
        if was == now {
            return;
        }
        let stale: Vec<TargetKey> =
            was.into_iter().chain(now).flat_map(|view| view.targets.iter().flat_map(expand_target)).collect();
        for key in &stale {
            self.last_published.remove(key);
        }
        if let Some(tick) = self.tick.as_mut() {
            tick.published.retain(|key| !stale.contains(key));
            tick.edited.push(edited.to_owned());
        }
    }

    fn forget_edited(&mut self, current: &[HclScheduleView]) {
        if self.published_from.as_deref() == Some(current) {
            for record in self.last_published.values_mut() {
                record.confirmed = false;
            }
            return;
        }
        self.last_published.clear();
        self.published_from = None;
    }
}

fn schedule_named<'v>(views: &'v [HclScheduleView], schedule_id: &str) -> Option<&'v HclScheduleView> {
    views.iter().find(|view| view.schedule_id == schedule_id)
}

struct SchedulerDeps {
    publisher: BusPublisher,
    bus_id: BusId,
    read_port: Arc<dyn HclSchedulerReadPort>,
    clock: Arc<dyn WallClock>,
    correlation: Arc<CorrelationIdAllocator>,
    config: HclConfig,
    counters: Arc<HclSchedulerCounters>,
    overrides: SharedOverrideLedger,
    role: Arc<dyn dali2rust_domain::registry::DaliSettingsReadPort>,
    hold: Arc<dali2rust_platform::firmware::MaintenanceHold>,
    liveness: Arc<dali2rust_platform::liveness::LivenessBeat>,
}

#[allow(clippy::too_many_arguments, reason = "one spawn site; the deps are grouped inside")]
pub fn spawn_hcl_scheduler_worker(
    rx: BusSubscriberRx,
    conf_rx: BusSubscriberRx,
    publisher: BusPublisher,
    bus_id: BusId,
    read_port: Arc<dyn HclSchedulerReadPort>,
    clock: Arc<dyn WallClock>,
    correlation: Arc<CorrelationIdAllocator>,
    config: HclConfig,
    counters: Arc<HclSchedulerCounters>,
    overrides: SharedOverrideLedger,
    liveness: Arc<dali2rust_platform::liveness::LivenessBeat>,
    role: Arc<dyn dali2rust_domain::registry::DaliSettingsReadPort>,
    hold: Arc<dali2rust_platform::firmware::MaintenanceHold>,
) -> std::thread::JoinHandle<()> {
    let deps = SchedulerDeps {
        publisher,
        bus_id,
        read_port,
        clock,
        correlation,
        config,
        counters,
        overrides,
        role,
        hold,
        liveness,
    };
    esp_thread::spawn_named_stack_in(
        c"hcl-scheduler",
        std_thread_stack::EVENT_WORKER_STACK,
        esp_thread::StackHome::ExternalOnXip,
        move || run_loop(rx, conf_rx, deps),
    )
}

fn drain_stale_confirmations(conf_rx: &BusSubscriberRx) {
    while conf_rx.try_recv().is_ok() {}
}

static WORKER_STACK: StackLowWater =
    StackLowWater::new("hcl-scheduler", std_thread_stack::EVENT_WORKER_STACK);

fn run_loop(rx: BusSubscriberRx, conf_rx: BusSubscriberRx, deps: SchedulerDeps) {
    let mut state = SchedulerState::new();
    let period = Duration::from_millis(deps.config.tick_period_ms);
    let mut next_tick = Instant::now();
    loop {
        if Instant::now() >= next_tick {
            run_tick(&mut state, &rx, &conf_rx, &deps);
            WORKER_STACK.note("tick");
            next_tick = Instant::now() + period;
        }
        let wait = next_tick
            .saturating_duration_since(Instant::now())
            .min(MAX_IDLE_WAIT);
        match deps.liveness.while_turning(|| rx.recv_timeout(wait)) {
            Ok(frame) => {
                apply_frame(&mut state, &deps, &frame);
                WORKER_STACK.note(frame_tag(&frame));
            }
            Err(std::sync::mpsc::RecvTimeoutError::Timeout) => WORKER_STACK.note("idle"),
            Err(std::sync::mpsc::RecvTimeoutError::Disconnected) => return,
        }
        drain_stale_confirmations(&conf_rx);
    }
}

fn frame_tag(frame: &BusFrame) -> &'static str {
    match frame {
        BusFrame::Event(envelope) => match &envelope.payload {
            BusEventPayload::HclScheduleChangedEvent(_) => "event:HclScheduleChanged",
            BusEventPayload::RuntimeStateChangedEvent(_) => "event:RuntimeStateChanged",
            _ => "event:other",
        },
        BusFrame::Command(_) => "command",
        BusFrame::Confirmation(_) => "confirmation",
    }
}

fn apply_frame(state: &mut SchedulerState, deps: &SchedulerDeps, frame: &BusFrame) {
    match frame {
        BusFrame::Event(envelope) => apply_event(state, deps, &envelope.payload),
        BusFrame::Command(envelope) => dispatch_scheduler_command(
            &envelope.payload,
            state,
            deps,
            envelope.meta.correlation_id,
        ),
        BusFrame::Confirmation(_) => {
            deps.counters.ignored_events.fetch_add(1, Ordering::Relaxed);
        }
    }
}

dali2rust_contracts::dispatch_bus_commands! {
    pub const HCL_SCHEDULER_HANDLED_COMMANDS;
    fn dispatch_scheduler_command(
        payload: &BusCommandPayload,
        state: &mut SchedulerState,
        deps: &SchedulerDeps,
        correlation_id: u64,
    );
    payload = payload;
    ignored = { deps.counters.ignored_commands.fetch_add(1, Ordering::Relaxed); };
    HclOverrideClearCommand(body) => handle_override_clear(deps, correlation_id, body),
    HclOverrideHoldCommand(body) => handle_override_hold(state, deps, correlation_id, body),
    HclOverrideResumeCommand(body) => handle_override_resume(deps, correlation_id, body),
}

fn handle_override_clear(deps: &SchedulerDeps, correlation_id: u64, body: &HclOverrideClearCommand) {
    let lifted = lock_ledger(&deps.overrides).clear_schedule(body.schedule_id.as_str());
    count_lifted(deps, lifted);
    confirm_override_command(deps, correlation_id, None);
}

fn handle_override_resume(deps: &SchedulerDeps, correlation_id: u64, body: &HclOverrideResumeCommand) {
    let adapter_id = body.registry_adapter_id;
    let removal = resume_removal(deps.read_port.as_ref(), adapter_id, body.target);
    let lifted = lock_ledger(&deps.overrides).resume(adapter_id, removal);
    count_lifted(deps, lifted);
    confirm_override_command(deps, correlation_id, None);
}

fn count_lifted(deps: &SchedulerDeps, lifted: usize) {
    if lifted > 0 {
        deps.counters
            .overrides_reset
            .fetch_add(lifted as u32, Ordering::Relaxed);
    }
}

fn handle_override_hold(
    state: &mut SchedulerState,
    deps: &SchedulerDeps,
    correlation_id: u64,
    body: &HclOverrideHoldCommand,
) {
    let Some(local) = deps.clock.local() else {
        confirm_override_command(deps, correlation_id, Some(HOLD_WITHOUT_CLOCK));
        return;
    };
    roll_over_ledger(state, deps, local.year_day);
    hold_covered_targets(state, deps, body, local);
    confirm_override_command(deps, correlation_id, None);
}

fn hold_covered_targets(
    state: &mut SchedulerState,
    deps: &SchedulerDeps,
    body: &HclOverrideHoldCommand,
    local: LocalCivilTime,
) {
    let read_port = deps.read_port.as_ref();
    for schedule in read_port.list_hcl_schedule_views() {
        if !runs_today(&schedule, local) {
            continue;
        }
        for target in schedule.targets.iter().flat_map(expand_target) {
            if hold_covers_target(read_port, body.registry_adapter_id, body.target, target) {
                let (at, cause) = (local.minutes_since_midnight, Causes::of_hold(body.target));
                hold_target(state, deps, &schedule.schedule_id, target, at, cause);
            }
        }
    }
}

fn hold_target(
    state: &mut SchedulerState,
    deps: &SchedulerDeps,
    schedule_id: &str,
    target: TargetKey,
    at_minutes: u16,
    cause: Causes,
) {
    if lock_ledger(&deps.overrides).suspend(schedule_id, target, at_minutes, cause) {
        deps.counters.overrides_started.fetch_add(1, Ordering::Relaxed);
    }
    state.stand_down(target);
}

fn confirm_override_command(deps: &SchedulerDeps, correlation_id: u64, refusal: Option<&str>) {
    let envelope = match refusal {
        None => build_confirmation_envelope(correlation_id, DeliveryStatus::Ok, 0, SOURCE_ID_UNSPECIFIED),
        Some(message) => build_confirmation_envelope_with_product_error(
            correlation_id,
            DeliveryStatus::ExecutionFailed,
            0,
            SOURCE_ID_UNSPECIFIED,
            Some((ErrorCode::Conflict, message)),
        ),
    };
    publish_or_drop(
        &deps.publisher,
        BusChannel::Confirmations,
        BusFrame::confirmation(envelope),
        "hcl-override-command",
    );
}

fn apply_event(state: &mut SchedulerState, deps: &SchedulerDeps, payload: &BusEventPayload) {
    match payload {
        BusEventPayload::HclScheduleChangedEvent(body) => apply_schedule_change(state, deps, body),
        BusEventPayload::RuntimeStateChangedEvent(body) => {
            suspend_hit_targets(state, deps, &runtime_commit(body));
        }
        _ => {
            deps.counters.ignored_events.fetch_add(1, Ordering::Relaxed);
        }
    }
}

fn apply_schedule_change(
    state: &mut SchedulerState,
    deps: &SchedulerDeps,
    body: &HclScheduleChangedEvent,
) {
    let current = sorted_schedules(deps);
    if state.tick.is_some() {
        state.edit_during_tick(body.schedule_id.as_str(), &current);
    } else {
        state.forget_edited(&current);
    }
    if body.removed {
        let lifted = lock_ledger(&deps.overrides).clear_schedule(body.schedule_id.as_str());
        count_lifted(deps, lifted);
    }
}

fn runtime_commit(body: &RuntimeStateChangedEvent) -> RuntimeCommit {
    RuntimeCommit {
        adapter_id: body.adapter_id,
        virtual_lamp_id: body.virtual_lamp_id,
        value_source: Some(body.commit_source),
        states: body.commit_dimensions,
        holds_hcl: body.commit_holds_hcl,
    }
}

fn suspend_hit_targets(state: &mut SchedulerState, deps: &SchedulerDeps, commit: &RuntimeCommit) {
    if !commit.overrides() {
        return;
    }
    let Some(local) = deps.clock.local() else {
        return;
    };
    roll_over_ledger(state, deps, local.year_day);
    let mut split = HitSplit::default();
    for schedule in deps.read_port.list_hcl_schedule_views() {
        if runs_today(&schedule, local) {
            split_targets(state, deps, commit, (&schedule, local), &mut split);
        }
    }
    for target in split.hit.into_iter().filter(|target| !split.spared.contains(target)) {
        state.stand_down(target);
    }
}

#[derive(Default)]
struct HitSplit {
    hit: Vec<TargetKey>,
    spared: Vec<TargetKey>,
}

fn split_targets(
    state: &SchedulerState,
    deps: &SchedulerDeps,
    commit: &RuntimeCommit,
    (schedule, local): (&HclScheduleView, LocalCivilTime),
    split: &mut HitSplit,
) {
    let driven = driven_dimensions(&schedule.points);
    for target in schedule.targets.iter().flat_map(expand_target).filter(|t| state.driven(t)) {
        if !commit_hits_target(deps.read_port.as_ref(), commit, target, driven) {
            split.spared.push(target);
            continue;
        }
        let (at, cause) = (local.minutes_since_midnight, Causes::of_commit(commit));
        if lock_ledger(&deps.overrides).suspend(&schedule.schedule_id, target, at, cause) {
            deps.counters.overrides_started.fetch_add(1, Ordering::Relaxed);
        }
        split.hit.push(target);
    }
}

fn roll_over_ledger(state: &mut SchedulerState, deps: &SchedulerDeps, year_day: u16) {
    let Some(cleared) = lock_ledger(&deps.overrides).roll_over_to(year_day) else {
        return;
    };
    if cleared > 0 {
        deps.counters
            .overrides_cleared
            .fetch_add(cleared as u32, Ordering::Relaxed);
    }
    state.last_published.clear();
}

fn tick_is_due(deps: &SchedulerDeps) -> Option<LocalCivilTime> {
    if !deps.role.dali_settings_view().application_active {
        return None;
    }
    let local = deps.clock.local();
    if local.is_none() {
        deps.counters
            .ticks_time_unsynced
            .fetch_add(1, Ordering::Relaxed);
    }
    local
}

fn held_for_maintenance(deps: &SchedulerDeps) -> bool {
    deps.hold.engaged()
}

fn run_tick(
    state: &mut SchedulerState,
    rx: &BusSubscriberRx,
    conf_rx: &BusSubscriberRx,
    deps: &SchedulerDeps,
) {
    deps.counters.ticks.fetch_add(1, Ordering::Relaxed);
    if held_for_maintenance(deps) {
        return;
    }
    let Some(local) = tick_is_due(deps) else {
        return;
    };
    let (fresh, tick_plan) = plan_tick(state, deps, local);
    let schedules = state.published_from.as_deref().unwrap_or_default();
    state.tick = Some(TickScope::planned(schedules, &fresh));
    let outcomes = publish_plan(rx, conf_rx, deps, &tick_plan.commands, state);
    WORKER_STACK.note("tick:publish");
    finish_tick(state, deps, fresh, &outcomes);
}

fn finish_tick(
    state: &mut SchedulerState,
    deps: &SchedulerDeps,
    fresh: Vec<DesiredEntry>,
    outcomes: &PublishOutcomes,
) {
    let tick = state.tick.take().unwrap_or_default();
    record_published(state, fresh, outcomes, &tick);
    if tick.cut {
        deps.counters.ticks_cut.fetch_add(1, Ordering::Relaxed);
    }
    if !tick.edited.is_empty() {
        state.published_from = Some(sorted_schedules(deps));
    }
}

fn plan_tick(
    state: &mut SchedulerState,
    deps: &SchedulerDeps,
    local: LocalCivilTime,
) -> (Vec<DesiredEntry>, TickPlan) {
    roll_over_ledger(state, deps, local.year_day);
    state.published_from = Some(sorted_schedules(deps));
    let schedules = state.published_from.as_deref().unwrap_or_default();
    let entries = coalesce(desired_entries(deps, schedules, local));
    WORKER_STACK.note("tick:desired");
    let fresh = unconfirmed_entries(state, entries);
    let tick_plan = plan(&fresh);
    if tick_plan.dropped > 0 {
        let dropped = tick_plan.dropped as u32;
        deps.counters.commands_dropped_cap.fetch_add(dropped, Ordering::Relaxed);
    }
    WORKER_STACK.note("tick:plan");
    (fresh, tick_plan)
}

fn record_published(
    state: &mut SchedulerState,
    fresh: Vec<DesiredEntry>,
    outcomes: &PublishOutcomes,
    tick: &TickScope,
) {
    for entry in fresh.into_iter().filter(|entry| !tick.planned_by_an_edited_schedule(&entry.key)) {
        if let Some(confirmed) = outcomes.get(&entry.key) {
            let record = PublishRecord { state: entry.state, confirmed };
            state.last_published.insert(entry.key, record);
        }
    }
    for key in &tick.stood_down {
        state.last_published.remove(key);
    }
}

fn unconfirmed_entries(state: &SchedulerState, entries: Vec<DesiredEntry>) -> Vec<DesiredEntry> {
    entries
        .into_iter()
        .filter(|entry| {
            !state
                .last_published
                .get(&entry.key)
                .is_some_and(|rec| rec.confirmed && rec.state.wire_equal(&entry.state))
        })
        .collect()
}

fn sorted_schedules(deps: &SchedulerDeps) -> Vec<HclScheduleView> {
    let mut schedules = deps.read_port.list_hcl_schedule_views();
    insertion_sort_by(&mut schedules, |a, b| a.schedule_id > b.schedule_id);
    schedules
}

fn desired_entries(
    deps: &SchedulerDeps,
    schedules: &[HclScheduleView],
    local: LocalCivilTime,
) -> Vec<DesiredEntry> {
    let desired = desired_states(schedules, local);
    let ledger = lock_ledger(&deps.overrides);
    desired
        .into_iter()
        .flat_map(|(index, schedule, desired)| {
            schedule
                .targets
                .iter()
                .flat_map(expand_target)
                .filter(|target| !ledger.is_suspended(&schedule.schedule_id, *target))
                .map(move |key| DesiredEntry { key, state: desired, schedule: index })
        })
        .collect()
}

#[inline(never)]
fn desired_states(
    schedules: &[HclScheduleView],
    local: LocalCivilTime,
) -> Vec<(usize, &HclScheduleView, DesiredState)> {
    let mut desired = Vec::with_capacity(schedules.len());
    for (index, schedule) in schedules.iter().enumerate() {
        if !runs_today(schedule, local) {
            continue;
        }
        if let Some(state) = desired_state(schedule, local) {
            desired.push((index, schedule, state));
        }
    }
    desired
}

fn runs_today(schedule: &HclScheduleView, local: LocalCivilTime) -> bool {
    local.weekday < DAYS_PER_WEEK
        && schedule.enabled
        && schedule.active_days_mask & (1u8 << local.weekday) != 0
}

fn desired_state(schedule: &HclScheduleView, local: LocalCivilTime) -> Option<DesiredState> {
    let location =
        Location::from_microdeg(schedule.latitude_microdeg, schedule.longitude_microdeg);
    let points = effective_points(
        &schedule.points,
        location,
        local.year_day,
        local.utc_offset_minutes,
    );
    evaluate(
        &points,
        i32::from(local.minutes_since_midnight),
        schedule.algorithm,
    )
}

fn publish_plan(
    rx: &BusSubscriberRx,
    conf_rx: &BusSubscriberRx,
    deps: &SchedulerDeps,
    commands: &[PlannedCommand],
    state: &mut SchedulerState,
) -> PublishOutcomes {
    let mut outcomes = PublishOutcomes::default();
    for (index, command) in commands.iter().enumerate() {
        if state.skips_in_tick(&command.key()) {
            continue;
        }
        let Some(confirmed) = publish_one(rx, conf_rx, deps, command, state) else {
            mark_unpublished_keys(&mut outcomes, &commands[index..]);
            break;
        };
        outcomes.merge(command.key(), confirmed);
    }
    outcomes
}

fn publish_one(
    rx: &BusSubscriberRx,
    conf_rx: &BusSubscriberRx,
    deps: &SchedulerDeps,
    command: &PlannedCommand,
    state: &mut SchedulerState,
) -> Option<bool> {
    let correlation_id = deps.correlation.next_id();
    let frame = BusFrame::command(command_envelope_for(deps, command, correlation_id));
    if deps.publisher.try_publish(BusChannel::Commands, frame) != PublishResult::Queued {
        deps.counters.ingress_rejections.fetch_add(1, Ordering::Relaxed);
        return None;
    }
    deps.counters.commands_published.fetch_add(1, Ordering::Relaxed);
    state.note_published(command.key());
    let timeout_ms = deps.config.command_timeout_ms;
    Some(wait_for_confirmation(rx, conf_rx, deps, correlation_id, timeout_ms, state))
}

fn mark_unpublished_keys(outcomes: &mut PublishOutcomes, unpublished: &[PlannedCommand]) {
    for command in unpublished {
        outcomes.demote(command.key());
    }
}

fn serve_inbox(rx: &BusSubscriberRx, deps: &SchedulerDeps, state: &mut SchedulerState) {
    while let Ok(frame) = rx.try_recv() {
        apply_frame(state, deps, &frame);
    }
}

fn command_envelope_for(
    deps: &SchedulerDeps,
    command: &PlannedCommand,
    correlation_id: u64,
) -> dali2rust_contracts::msg::CommandEnvelope {
    let key = command.key();
    match command {
        PlannedCommand::TargetState { setpoint, .. } => command_envelope(
            SOURCE_ID_UNSPECIFIED,
            correlation_id,
            deps.bus_id.0,
            Some(Origin::Hcl),
            DaliSetTargetStateCommand {
                scope: command.dali_scope(),
                virtual_lamp_id: 0,
                short_address: 0,
                group_id: key.group_id,
                setpoint: setpoint.clone(),
                registry_adapter_id: key.adapter_id,
                hold_hcl: true,
            },
        ),
        PlannedCommand::RecallLastActive { .. } => command_envelope(
            SOURCE_ID_UNSPECIFIED,
            correlation_id,
            deps.bus_id.0,
            Some(Origin::Hcl),
            DaliRecallLastActiveLevelCommand {
                registry_adapter_id: key.adapter_id,
                scope: key.scope,
                group_id: match key.scope {
                    dali2rust_contracts::msg::HclTargetScope::Group => Some(key.group_id),
                    dali2rust_contracts::msg::HclTargetScope::Broadcast => None,
                },
            },
        ),
    }
}

fn wait_for_confirmation(
    rx: &BusSubscriberRx,
    conf_rx: &BusSubscriberRx,
    deps: &SchedulerDeps,
    correlation_id: u64,
    timeout_ms: u64,
    state: &mut SchedulerState,
) -> bool {
    let deadline = Instant::now() + Duration::from_millis(timeout_ms);
    loop {
        let remaining = deadline.saturating_duration_since(Instant::now());
        if remaining.is_zero() {
            return timed_out(deps);
        }
        let slice = remaining.min(CONFIRMATION_POLL_SLICE);
        let received = deps.liveness.while_turning(|| conf_rx.recv_timeout(slice));
        serve_inbox(rx, deps, state);
        match received {
            Ok(BusFrame::Confirmation(envelope)) if envelope.meta.correlation_id == correlation_id => {
                return confirmed_ok(deps, envelope.status);
            }
            Err(std::sync::mpsc::RecvTimeoutError::Disconnected) => return timed_out(deps),
            _ => {}
        }
    }
}

fn timed_out(deps: &SchedulerDeps) -> bool {
    deps.counters.command_timeouts.fetch_add(1, Ordering::Relaxed);
    false
}

fn confirmed_ok(deps: &SchedulerDeps, status: DeliveryStatus) -> bool {
    if status == DeliveryStatus::Ok {
        return true;
    }
    deps.counters.command_failures.fetch_add(1, Ordering::Relaxed);
    false
}

#[cfg(test)]
mod tests {
    use super::*;

    #[test]
    fn an_ingress_break_between_a_pairs_halves_unconfirms_the_key_but_keeps_it_driven() {
        let pair_key = TargetKey {
            adapter_id: 0,
            scope: dali2rust_contracts::msg::HclTargetScope::Group,
            group_id: 3,
        };
        let undriven_key = TargetKey {
            adapter_id: 0,
            scope: dali2rust_contracts::msg::HclTargetScope::Group,
            group_id: 5,
        };
        let mut outcomes = PublishOutcomes::default();
        outcomes.merge(pair_key, true);
        mark_unpublished_keys(
            &mut outcomes,
            &[
                PlannedCommand::RecallLastActive { key: pair_key },
                PlannedCommand::RecallLastActive { key: undriven_key },
            ],
        );
        assert_eq!(
            outcomes.get(&pair_key),
            Some(false),
            "a partially-published entry is driven but not confirmed"
        );
        assert!(
            outcomes.get(&undriven_key).is_none(),
            "an entry nothing was published for must not arm the override gate"
        );
    }

    #[test]
    fn a_stand_down_between_ticks_leaves_nothing_for_a_tick_to_carry() {
        let key = TargetKey {
            adapter_id: 0,
            scope: dali2rust_contracts::msg::HclTargetScope::Group,
            group_id: 3,
        };
        let mut state = SchedulerState::new();
        state.stand_down(key);
        assert!(state.tick.is_none(), "a hold between ticks, as on a standby, keeps no list");

        state.tick = Some(TickScope::default());
        state.stand_down(key);
        let stood_down = state.tick.take().map(|tick| tick.stood_down);
        assert_eq!(stood_down, Some(vec![key]), "a tick in progress remembers what to strip");
    }
}
