ishergin/oxidali/crates/dali2rust-bsp/src/esp32p4/eth.rs

use core::ffi::{c_char, c_void, CStr};
use core::ptr;
use std::ffi::CString;
use std::sync::atomic::{AtomicBool, AtomicU32, Ordering};

use esp_idf_svc::sys::{self, esp, EspError};

use dali2rust_platform::net::{mac_text, node_name, LinkStats, LinkStatus, NetworkLink};

use super::emac_dma::{decode_missed_frames, MISSED_FRAMES_WORD};
use super::pins;

const PHY_ADDR_AUTO: i32 = -1;

const PHY_RESET_TIMEOUT_MS: u32 = 100;
const PHY_AUTONEG_TIMEOUT_MS: u32 = 4_000;

const EMAC_RX_TASK_STACK: u32 = 4_096;
const EMAC_RX_TASK_PRIO: u32 = 15;

static COUNTERS: Counters = Counters::new();

static RX_FRAMES_IN_PSRAM: AtomicBool = AtomicBool::new(true);

pub fn keep_rx_frames_internal() {
    RX_FRAMES_IN_PSRAM.store(false, Ordering::Relaxed);
}

pub fn rx_frames_in_psram() -> bool {
    RX_FRAMES_IN_PSRAM.load(Ordering::Relaxed)
}

unsafe extern "C" {
    static EMAC_DMA: u32;
}

struct Counters {
    rx_packets: AtomicU32,
    tx_packets: AtomicU32,
    rx_bytes: AtomicU32,
    tx_bytes: AtomicU32,
    rx_dropped: AtomicU32,
    tx_dropped: AtomicU32,
    rx_ring_overruns: AtomicU32,
    rx_fifo_overflows: AtomicU32,
    link_up_events: AtomicU32,
}

impl Counters {
    const fn new() -> Self {
        Self {
            rx_packets: AtomicU32::new(0),
            tx_packets: AtomicU32::new(0),
            rx_bytes: AtomicU32::new(0),
            tx_bytes: AtomicU32::new(0),
            rx_dropped: AtomicU32::new(0),
            tx_dropped: AtomicU32::new(0),
            rx_ring_overruns: AtomicU32::new(0),
            rx_fifo_overflows: AtomicU32::new(0),
            link_up_events: AtomicU32::new(0),
        }
    }

    fn add(counter: &AtomicU32, n: u32) {
        counter.fetch_add(n, Ordering::Relaxed);
    }
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
